gowenrw/hom3c0ming_badge/3D/FlashForgeAdv3/my_flower_profile-09.jpg

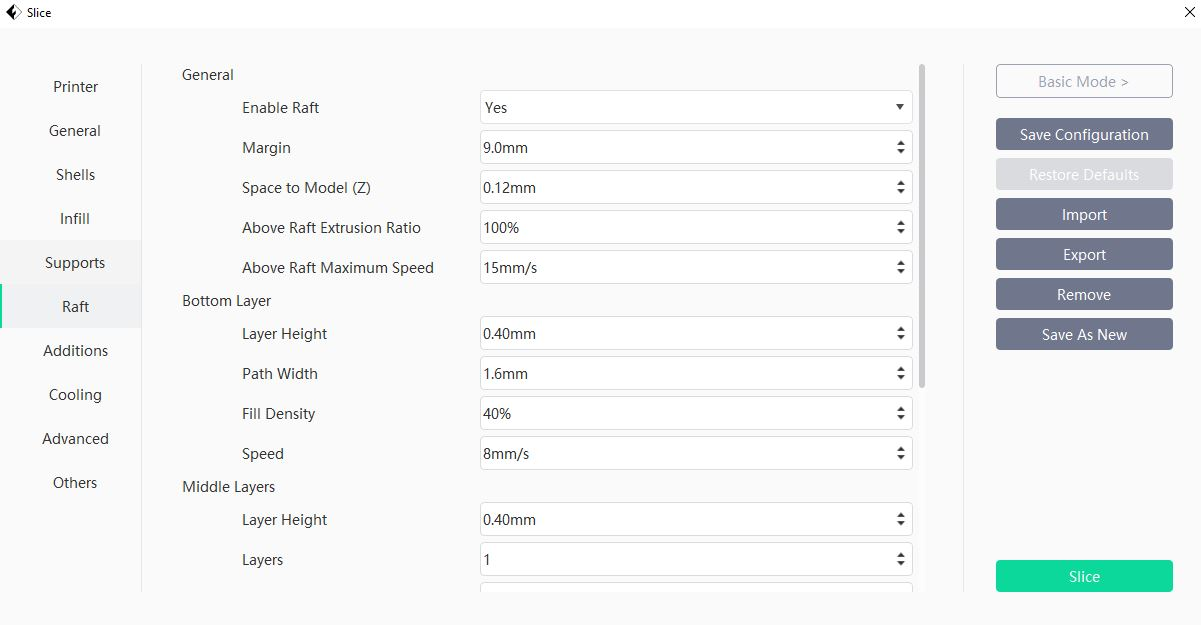
3D/FlashForgeAdv3/my_flower_profile-09.jpg
