gowenrw/hom3c0ming_badge/3D/Rose_LED_Cover_w_Leaves_back.jpg

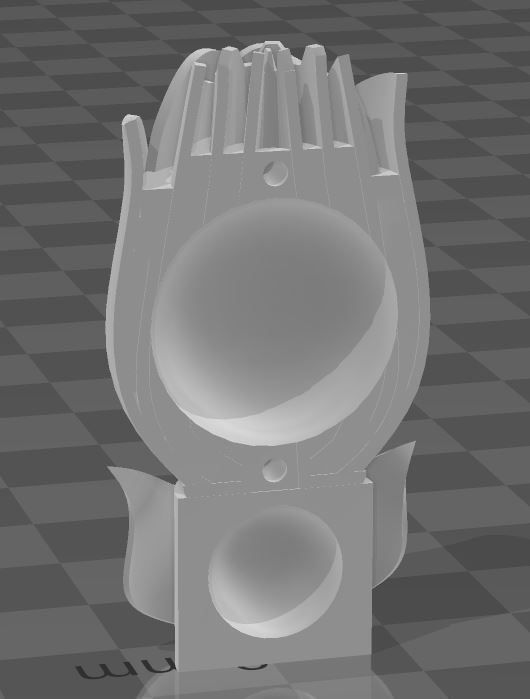
3D/Rose_LED_Cover_w_Leaves_back.jpg
