gowenrw/hom3c0ming_badge/3D/Rose_LED_Cover_w_Leaves_front.jpg

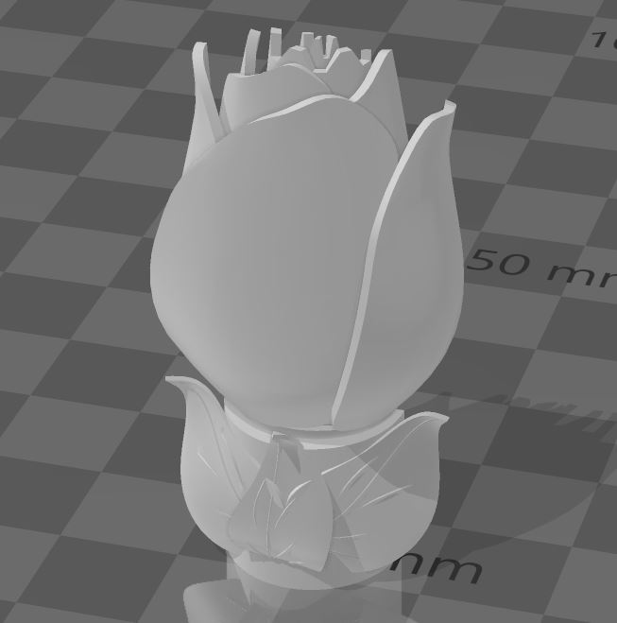
3D/Rose_LED_Cover_w_Leaves_front.jpg
