gowenrw/hom3c0ming_badge/art/Boutonniere_front-1-01.jpg

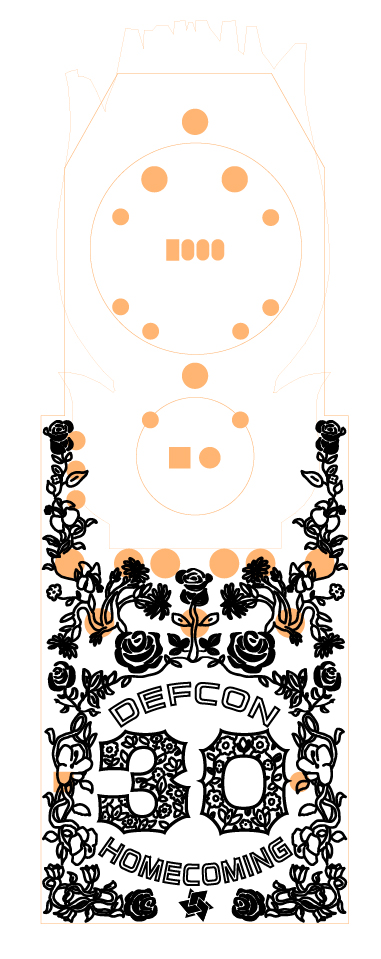
art/Boutonniere_front-1-01.jpg
