gowenrw/hom3c0ming_badge/art/Corsage_front-1-FlowerFace.jpg

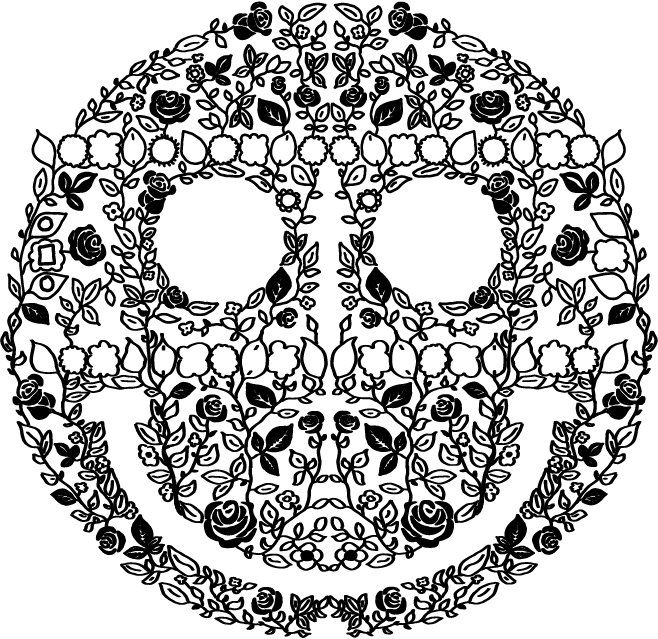
art/Corsage_front-1-FlowerFace.jpg
