gowenrw/hom3c0ming_badge/art/Corsage_front-2-HomeComing.jpg

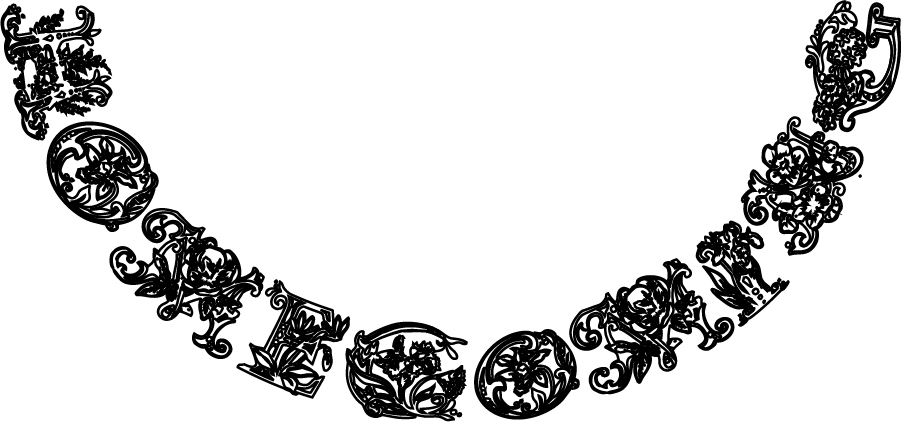
art/Corsage_front-2-HomeComing.jpg
