gowenrw/hom3c0ming_badge/art/Corsage_front-3-MLine.jpg

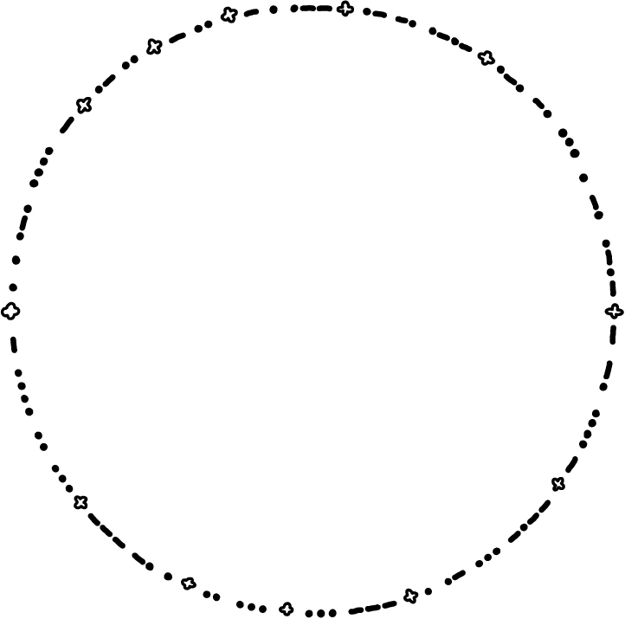
art/Corsage_front-3-MLine.jpg
