gowenrw/hom3c0ming_badge/art/Corsage_front-4-FlowersRightSide.jpg

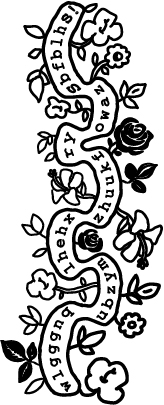
art/Corsage_front-4-FlowersRightSide.jpg
