gowenrw/hom3c0ming_badge/art/Corsage_front-5-FlowersBottom.jpg

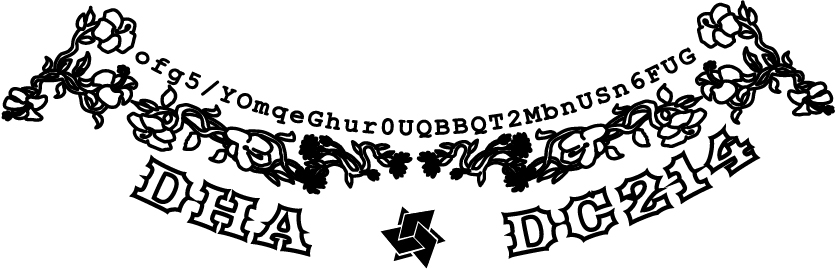
art/Corsage_front-5-FlowersBottom.jpg
