gowenrw/hom3c0ming_badge/art/Elliott_Flowers_2022-06-14_163128.jpg

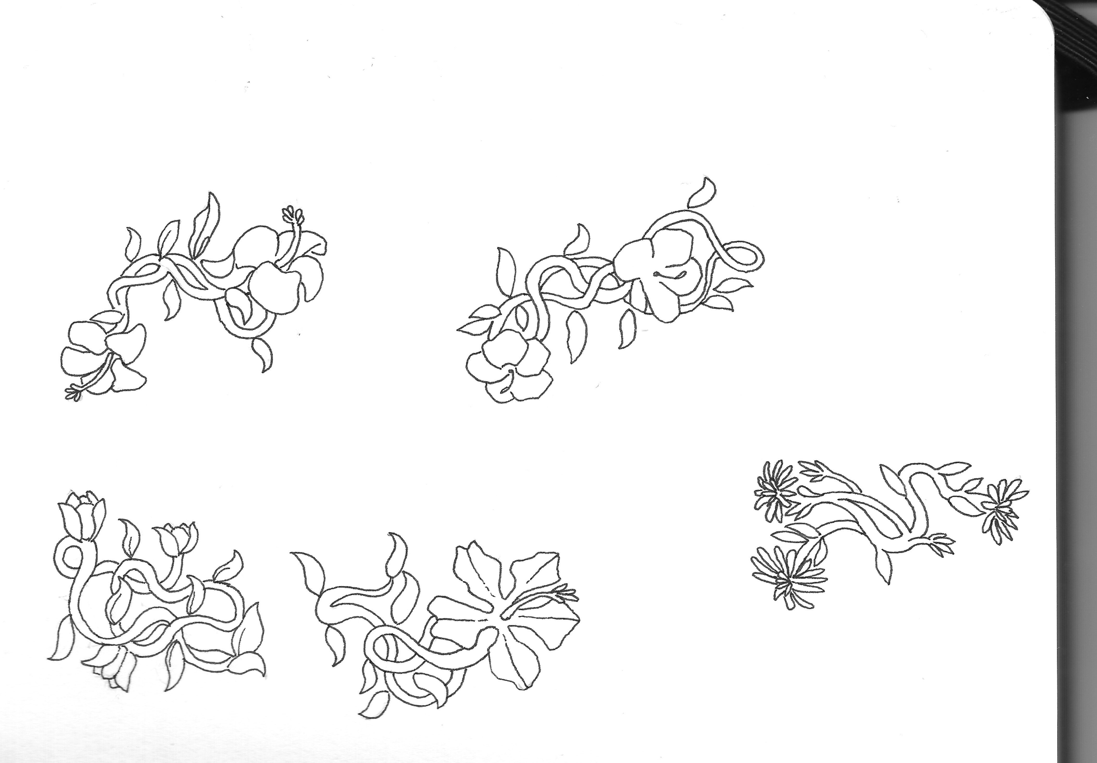
art/Elliott_Flowers_2022-06-14_163128.jpg
