gowenrw/hom3c0ming_badge/art/Hom3C0ming_Sticker-1-01.jpg

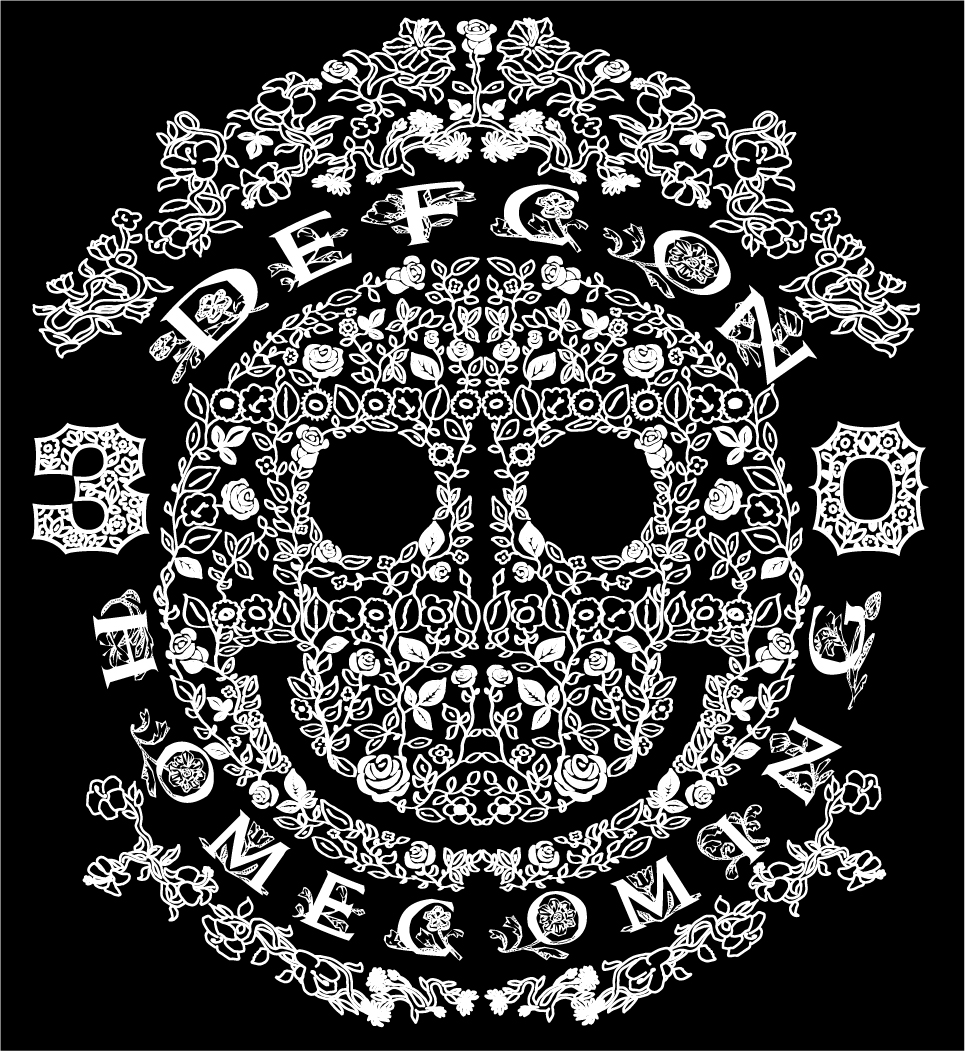
art/Hom3C0ming_Sticker-1-01.jpg
