gowenrw/hom3c0ming_badge/art/Hom3C0ming_Sticker-1PS.png

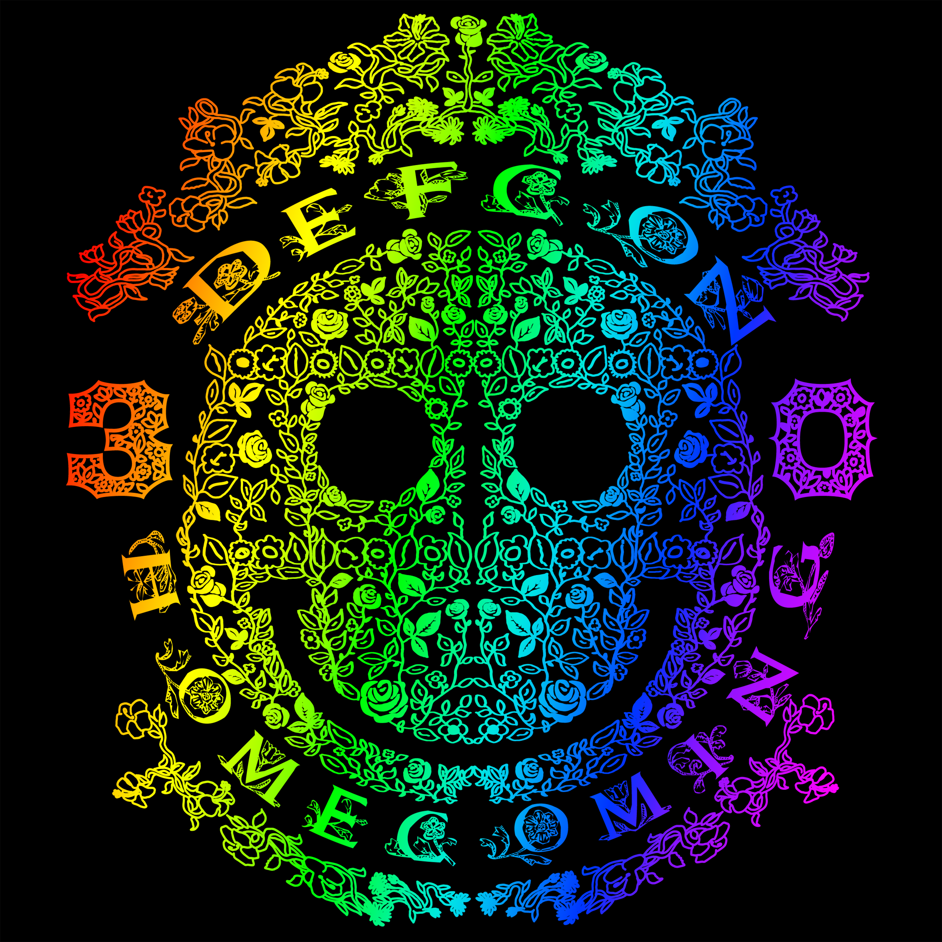
art/Hom3C0ming_Sticker-1PS.png
