gowenrw/hom3c0ming_badge/art/inspiration/20-207884_ivy-vine-drawing-at-getdrawings-ivy-vines-black.png

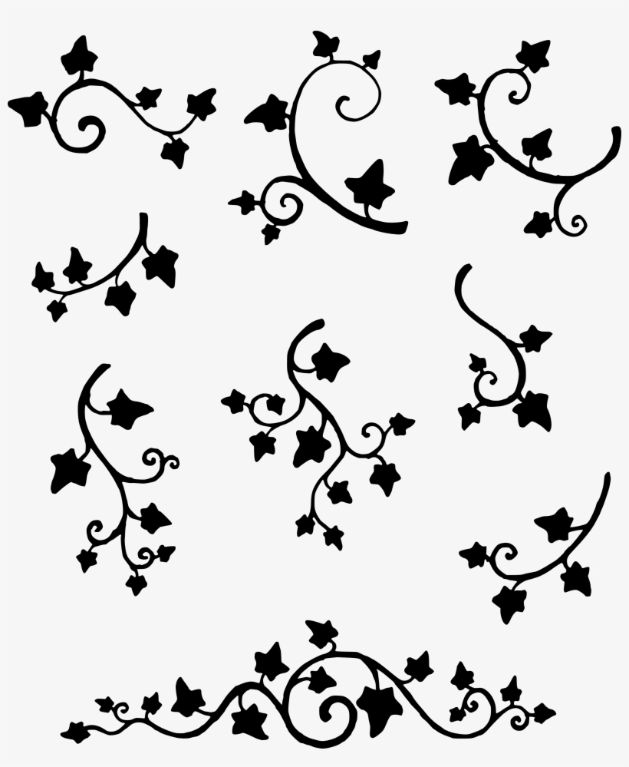
art/inspiration/20-207884_ivy-vine-drawing-at-getdrawings-ivy-vines-black.png
