gowenrw/hom3c0ming_badge/art/inspiration/beautiful-rose-vine-line-art-drawing-on-white-background-2GN6FTX.jpg

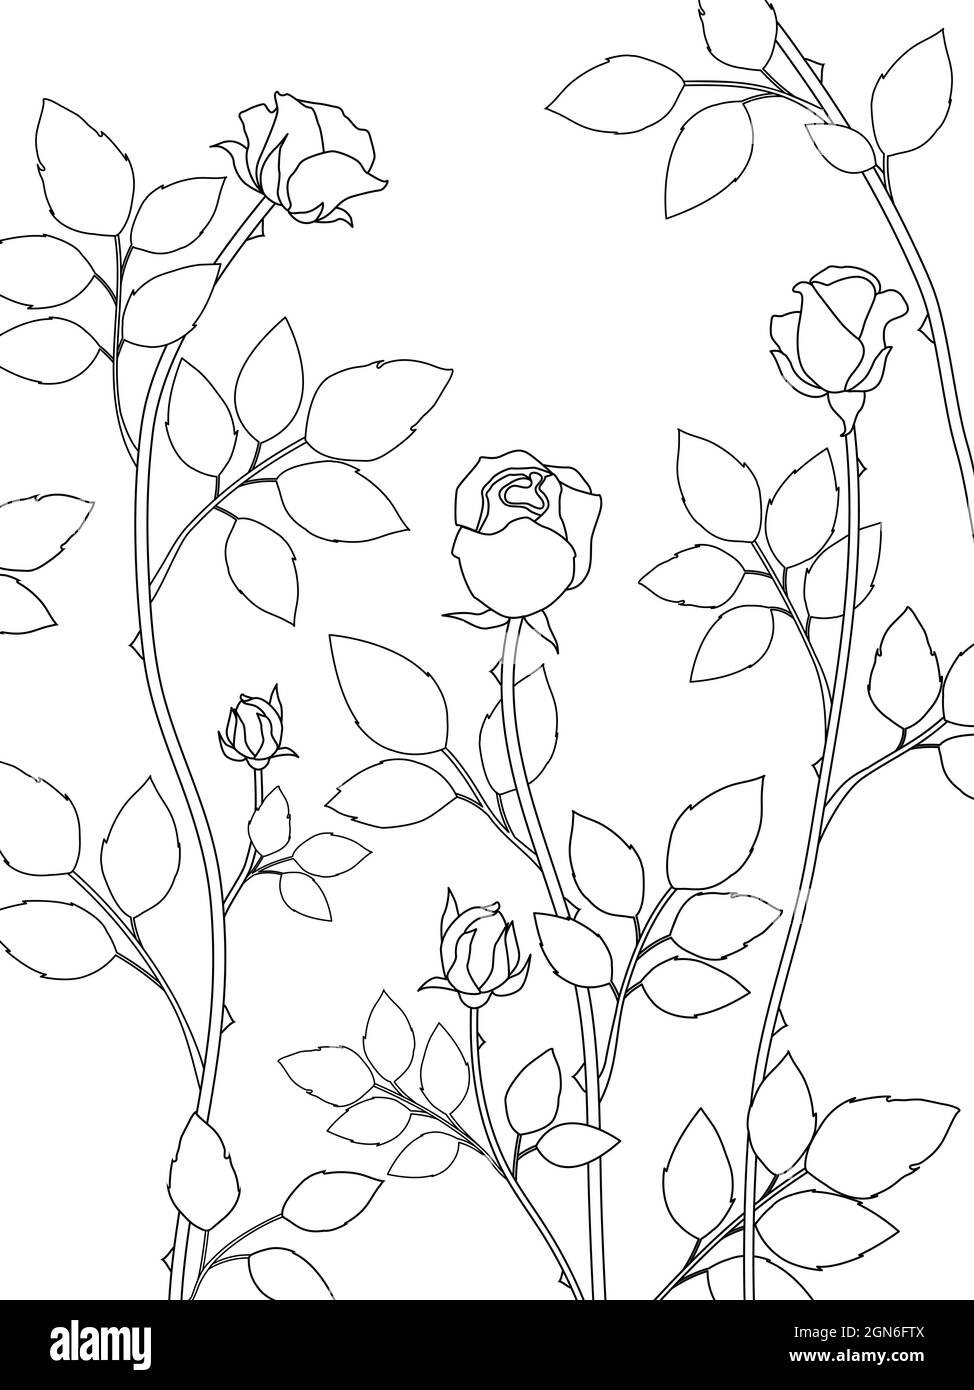
art/inspiration/beautiful-rose-vine-line-art-drawing-on-white-background-2GN6FTX.jpg
