gowenrw/hom3c0ming_badge/art/inspiration/e7fd83ab4b675ca70f8ec98111396026.jpg

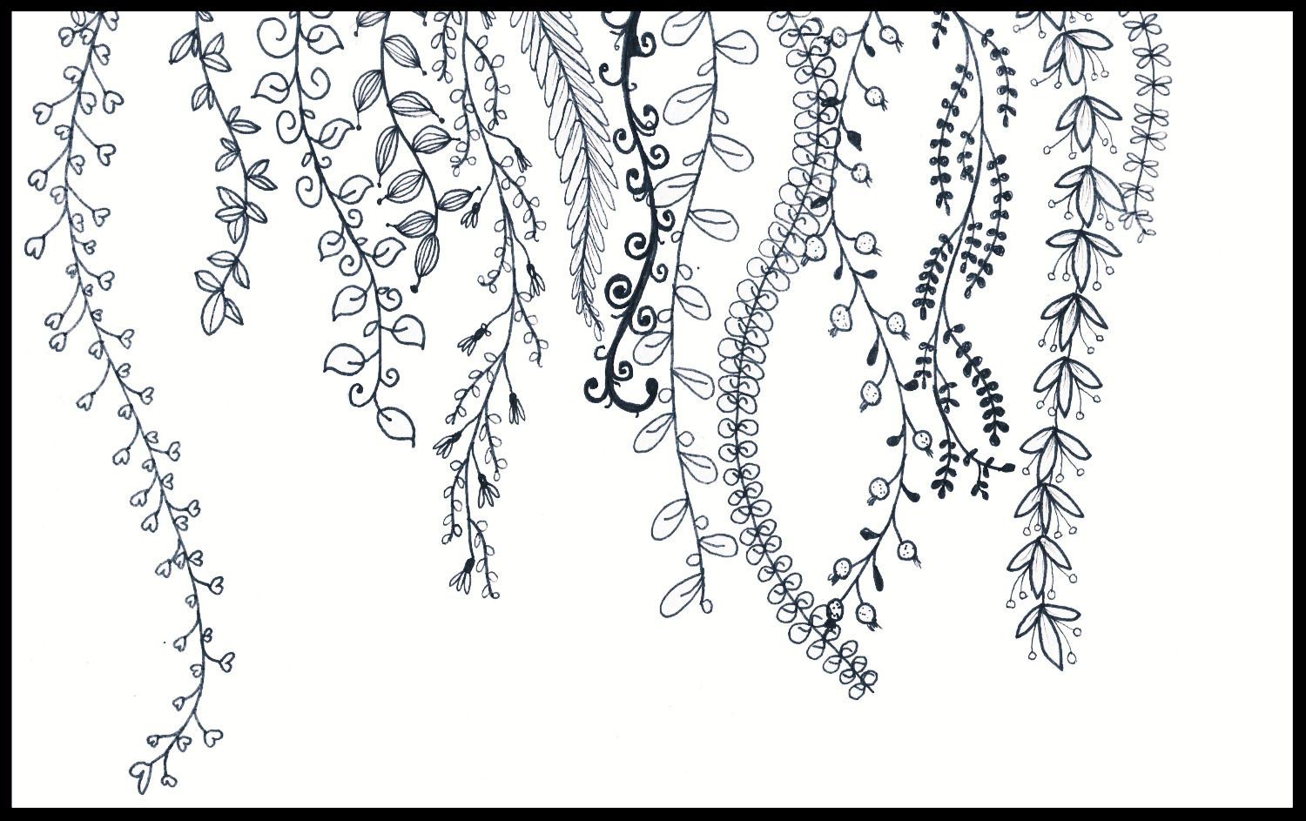
art/inspiration/e7fd83ab4b675ca70f8ec98111396026.jpg
