gowenrw/hom3c0ming_badge/art/inspiration/images.png

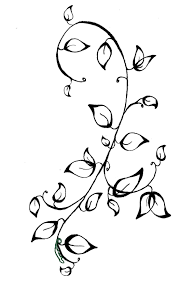
art/inspiration/images.png
