gowenrw/hom3c0ming_badge/art/Lanyard_Proof-uspv-62c86421a04712112495465-1657300001.png

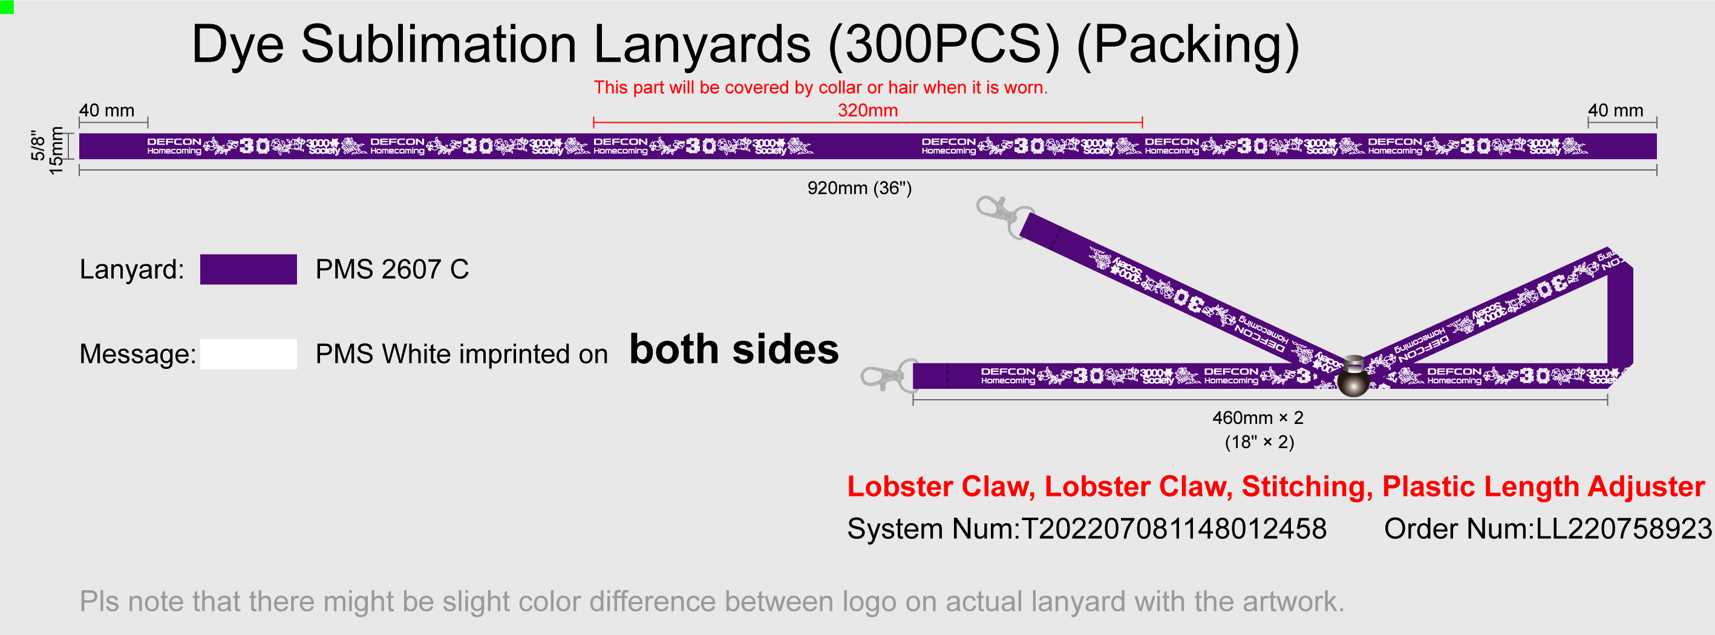
art/Lanyard_Proof-uspv-62c86421a04712112495465-1657300001.png
