gowenrw/hom3c0ming_badge/docs/images/20220730_111540-DatA55.jpg

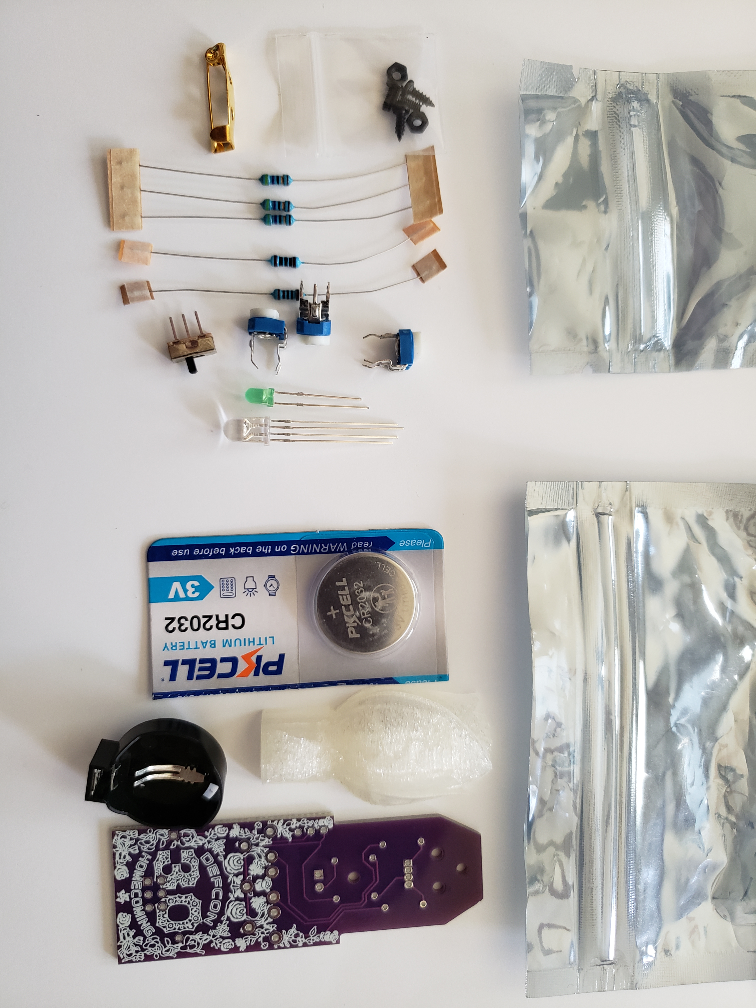
docs/images/20220730_111540-DatA55.jpg
