gowenrw/hom3c0ming_badge/eda/hom3c0ming_boutonniere/snapshots/hom3c0ming_boutonniere_back.jpg

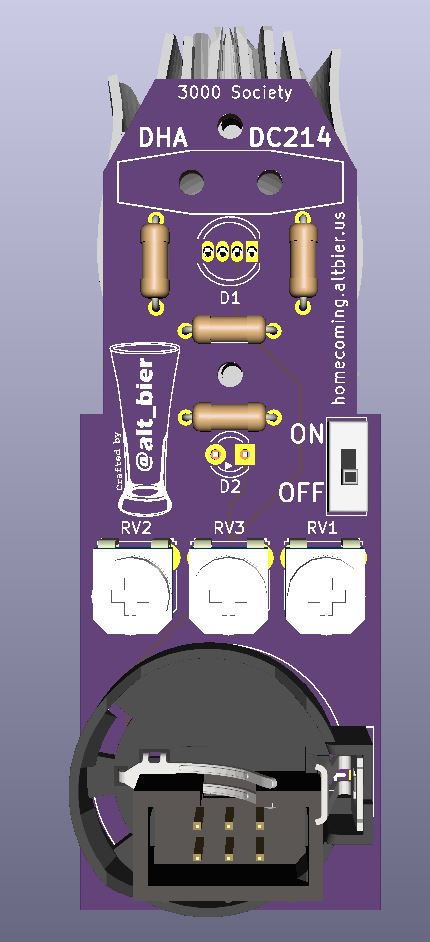
eda/hom3c0ming_boutonniere/snapshots/hom3c0ming_boutonniere_back.jpg
