gowenrw/hom3c0ming_badge/eda/hom3c0ming_corsage/snapshots/20220705_151704.jpg

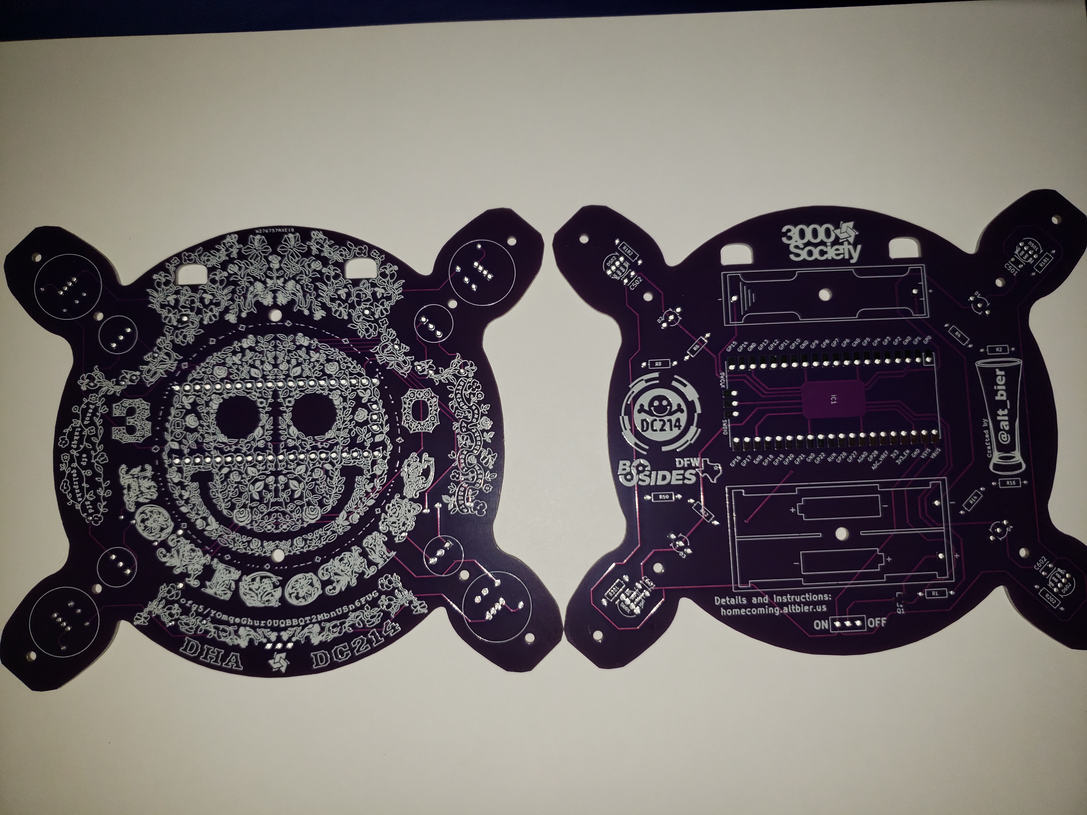
eda/hom3c0ming_corsage/snapshots/20220705_151704.jpg
