gowenrw/hom3c0ming_badge/eda/hom3c0ming_corsage/snapshots/hom3c0ming_corsage_back.jpg

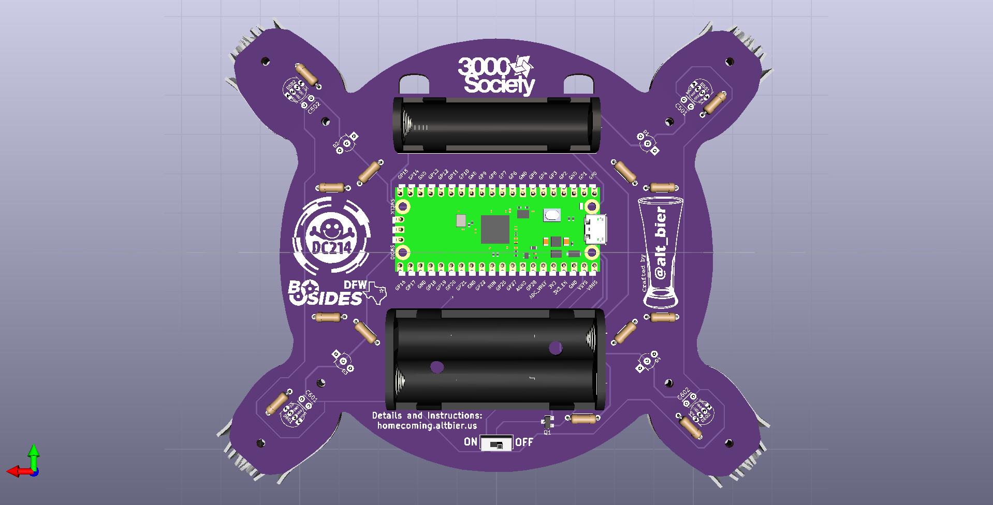
eda/hom3c0ming_corsage/snapshots/hom3c0ming_corsage_back.jpg
