gowenrw/hom3c0ming_badge/eda/hom3c0ming_boutonniere/3d_models/PinHeader_1x08_P2.54mm_Horizontal.step

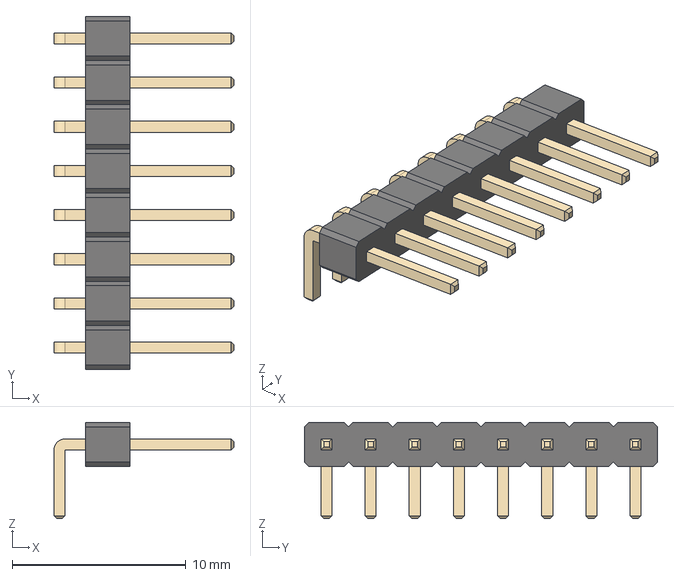
[picture p76: CAD file, 2022-07-30]
eda/hom3c0ming_boutonniere/3d_models/PinHeader_1x08_P2.54mm_Horizontal.step
10.4 x 20.3 x 5.54 mm
