gowenrw/hom3c0ming_badge/eda/hom3c0ming_corsage/3d_models/C_Rect_L4.6mm_W2.0mm_P2.50mm_MKS02_FKP02.step

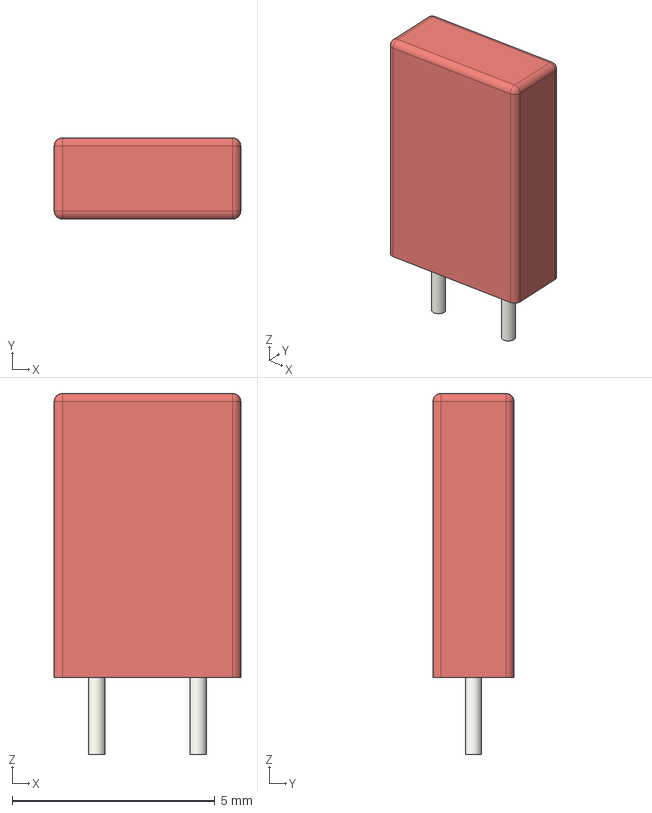
[picture p77: CAD file, 2022-07-30]
eda/hom3c0ming_corsage/3d_models/C_Rect_L4.6mm_W2.0mm_P2.50mm_MKS02_FKP02.step
4.60 x 2.00 x 8.90 mm
