gowenrw/hom3c0ming_badge/art/Corsage_front-5-FlowersBottom.dxf

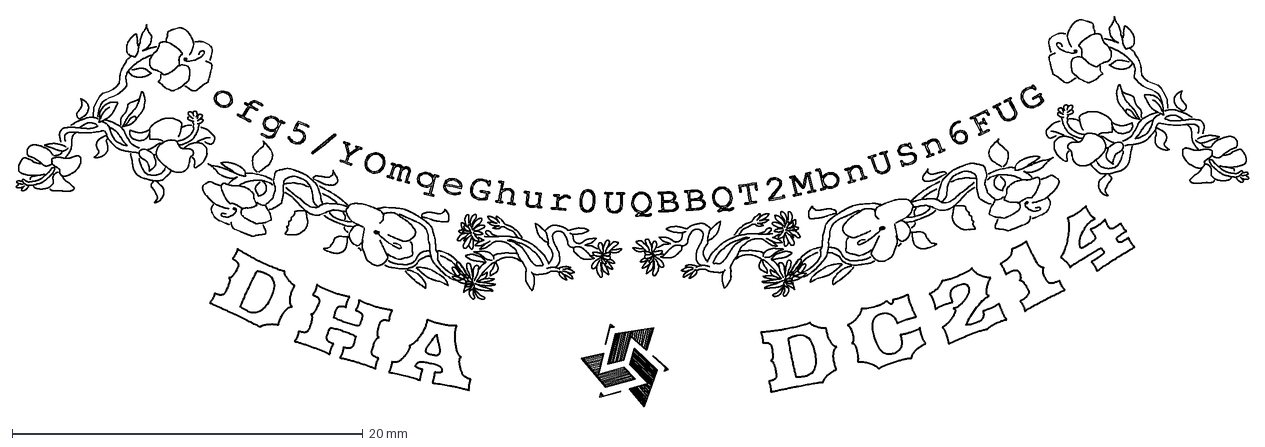
[picture p78: CAD file, 2022-07-30]
art/Corsage_front-5-FlowersBottom.dxf
70.3 x 22.3 mm
