gowenrw/hom3c0ming_badge/eda/hom3c0ming_boutonniere/3d_models/SOT-23.step

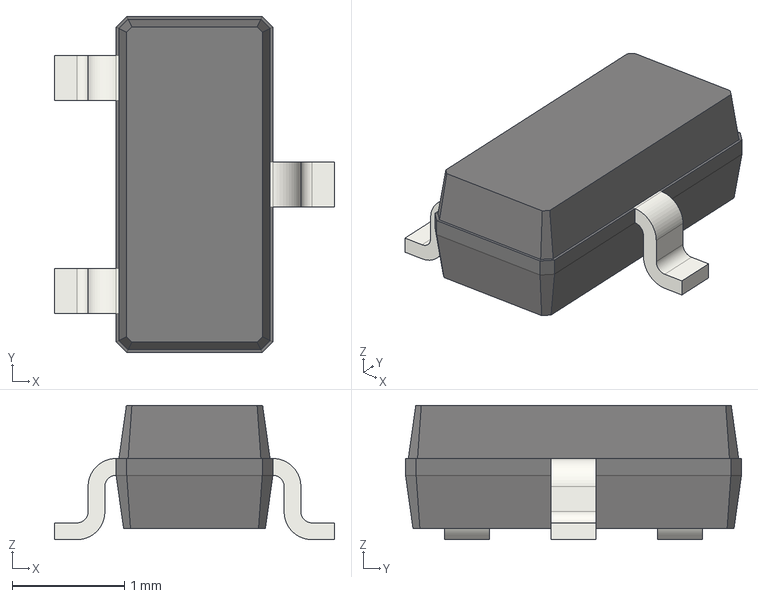
[picture p79: CAD file, 2022-07-30]
eda/hom3c0ming_boutonniere/3d_models/SOT-23.step
2.50 x 3.00 x 1.20 mm
