gowenrw/hom3c0ming_badge/eda/hom3c0ming_corsage/3d_models/LED_0805_2012Metric_Castellated.step

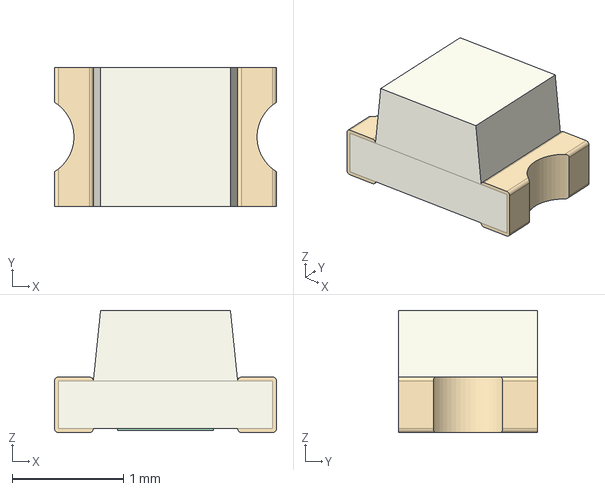
[picture p80: CAD file, 2022-07-30]
eda/hom3c0ming_corsage/3d_models/LED_0805_2012Metric_Castellated.step
2.00 x 1.25 x 1.10 mm
