gowenrw/hom3c0ming_badge/eda/hom3c0ming_boutonniere/3d_models/LED_D8.0mm.step

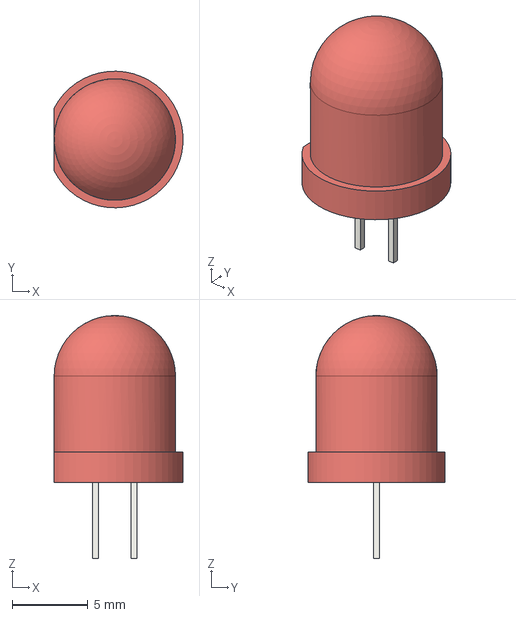
[picture p81: CAD file, 2022-07-30]
eda/hom3c0ming_boutonniere/3d_models/LED_D8.0mm.step
8.49 x 9.00 x 16.0 mm
