gowenrw/hom3c0ming_badge/eda/hom3c0ming_corsage/3d_models/SW_PUSH_6mm.step

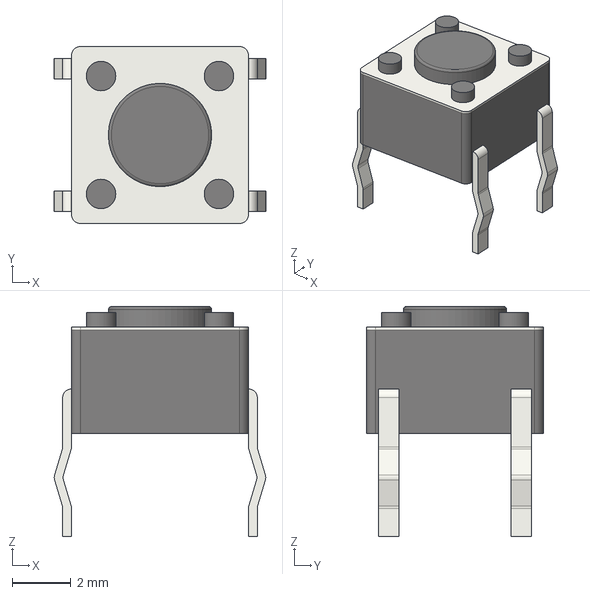
[picture p82: CAD file, 2022-07-30]
eda/hom3c0ming_corsage/3d_models/SW_PUSH_6mm.step
7.17 x 6.00 x 7.80 mm
