gowenrw/hom3c0ming_badge/eda/hom3c0ming_corsage/3d_models/PinSocket_1x05_P2.54mm_Horizontal.step

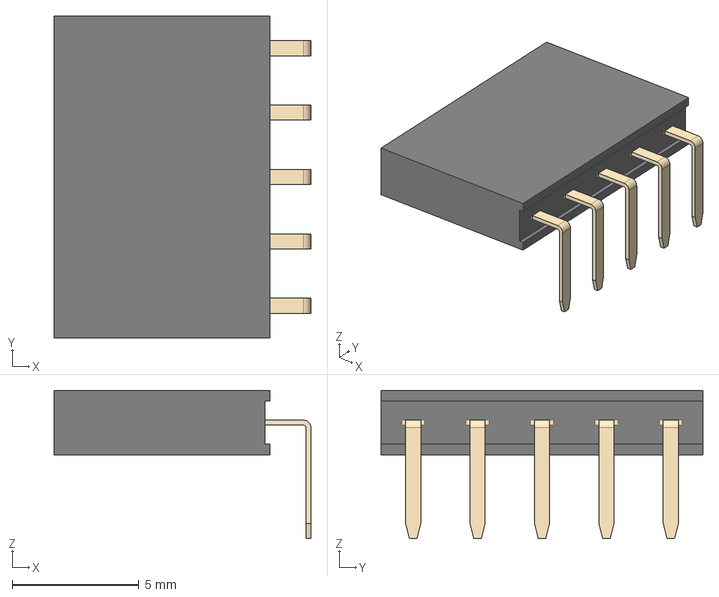
[picture p84: CAD file, 2022-07-30]
eda/hom3c0ming_corsage/3d_models/PinSocket_1x05_P2.54mm_Horizontal.step
10.1 x 12.7 x 5.84 mm
