gowenrw/hom3c0ming_badge/eda/hom3c0ming_boutonniere/3d_models/PinHeader_1x07_P2.54mm_Vertical.step

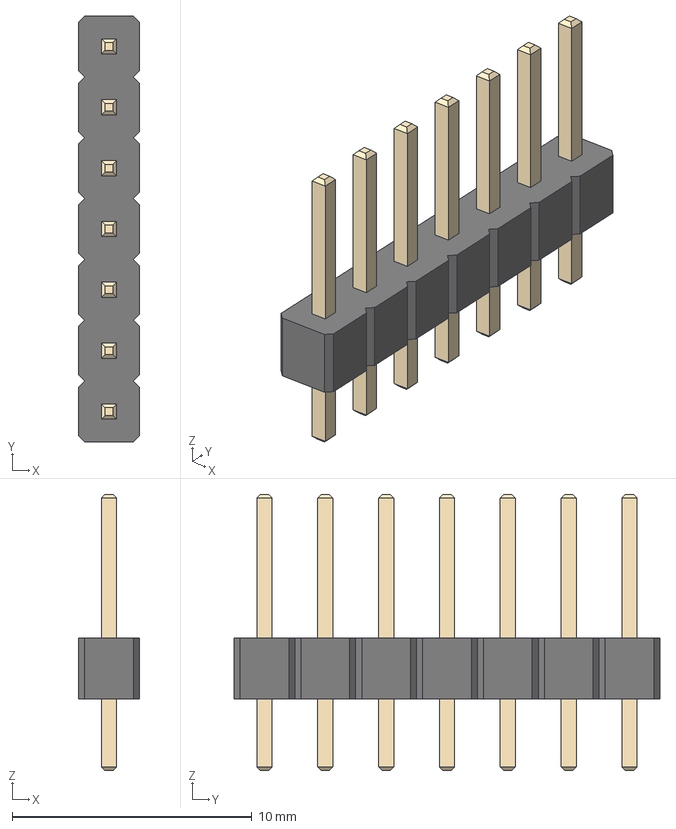
[picture p85: CAD file, 2022-07-30]
eda/hom3c0ming_boutonniere/3d_models/PinHeader_1x07_P2.54mm_Vertical.step
2.54 x 17.8 x 11.5 mm
