gowenrw/hom3c0ming_badge/eda/hom3c0ming_corsage/3d_models/PinHeader_1x07_P2.54mm_Horizontal.step

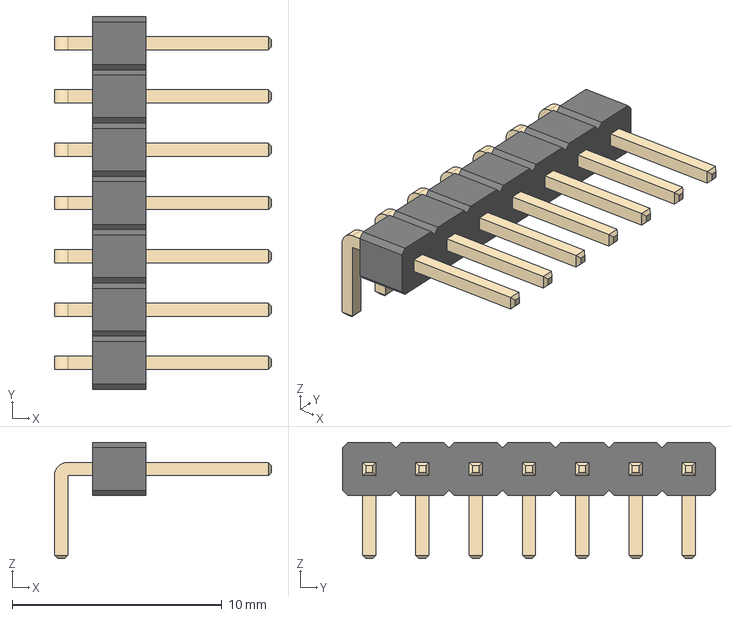
[picture p86: CAD file, 2022-07-30]
eda/hom3c0ming_corsage/3d_models/PinHeader_1x07_P2.54mm_Horizontal.step
10.4 x 17.8 x 5.54 mm
