gowenrw/hom3c0ming_badge/eda/hom3c0ming_boutonniere/3d_models/PinHeader_1x10_P2.54mm_Horizontal.step

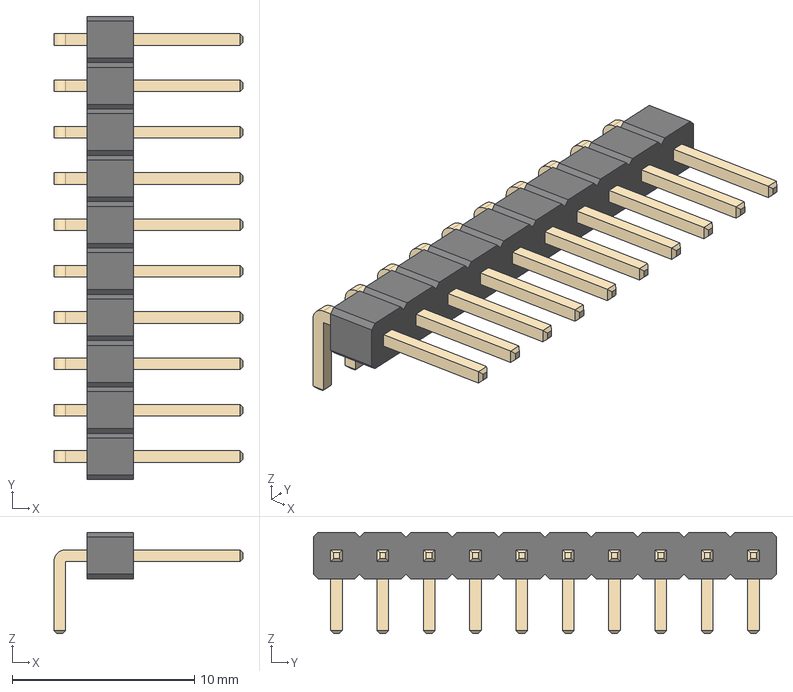
[picture p87: CAD file, 2022-07-30]
eda/hom3c0ming_boutonniere/3d_models/PinHeader_1x10_P2.54mm_Horizontal.step
10.4 x 25.4 x 5.54 mm
