gowenrw/hom3c0ming_badge/eda/hom3c0ming_boutonniere/3d_models/PinHeader_1x20_P2.54mm_Vertical.step

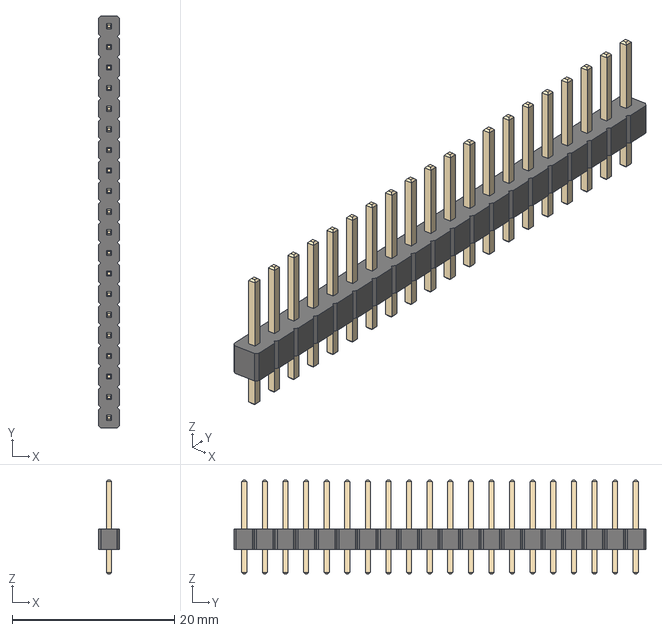
[picture p88: CAD file, 2022-07-30]
eda/hom3c0ming_boutonniere/3d_models/PinHeader_1x20_P2.54mm_Vertical.step
2.54 x 50.8 x 11.5 mm
