gowenrw/hom3c0ming_badge/eda/hom3c0ming_corsage/3d_models/PinHeader_1x06_P2.54mm_Horizontal.step

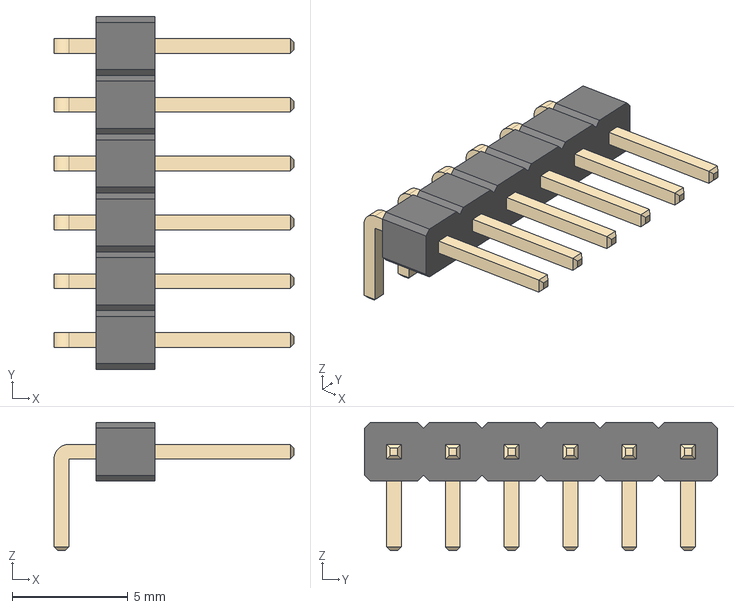
[picture p89: CAD file, 2022-07-30]
eda/hom3c0ming_corsage/3d_models/PinHeader_1x06_P2.54mm_Horizontal.step
10.4 x 15.2 x 5.54 mm
