gowenrw/hom3c0ming_badge/eda/hom3c0ming_corsage/3d_models/C_Disc_D3.0mm_W2.0mm_P2.50mm.step

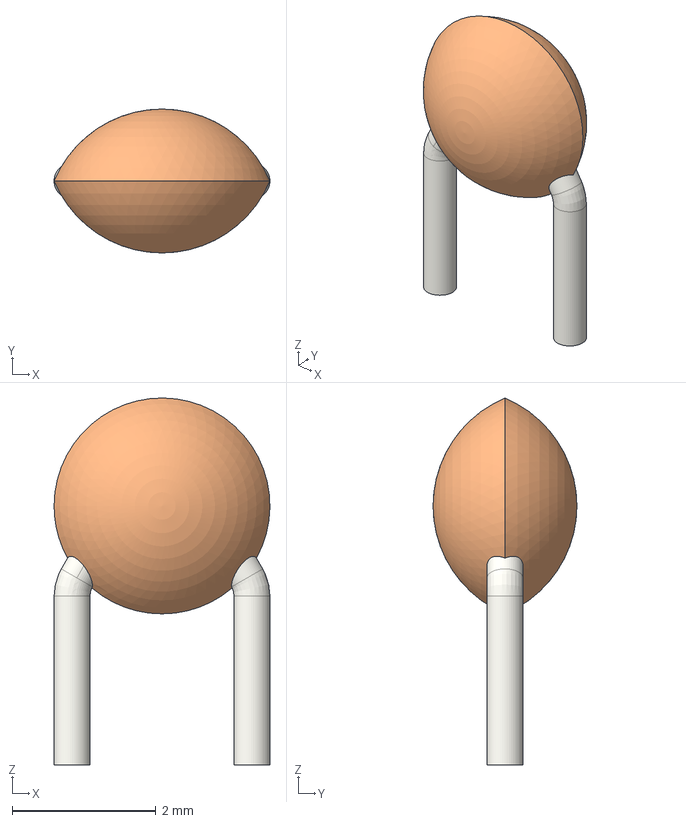
[picture p91: CAD file, 2022-07-30]
eda/hom3c0ming_corsage/3d_models/C_Disc_D3.0mm_W2.0mm_P2.50mm.step
3.00 x 2.00 x 5.10 mm
