gowenrw/hom3c0ming_badge/eda/hom3c0ming_corsage/3d_models/PinHeader_1x03_P2.54mm_Horizontal.step

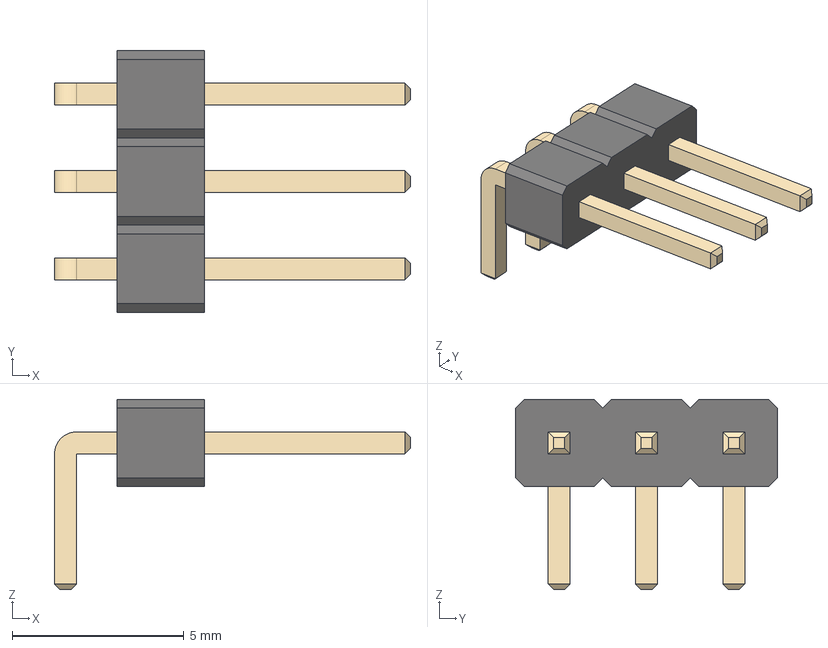
[picture p92: CAD file, 2022-07-30]
eda/hom3c0ming_corsage/3d_models/PinHeader_1x03_P2.54mm_Horizontal.step
10.4 x 7.62 x 5.54 mm
