gowenrw/hom3c0ming_badge/eda/hom3c0ming_corsage/3d_models/R_Axial_DIN0204_L3.6mm_D1.6mm_P5.08mm_Horizontal.step

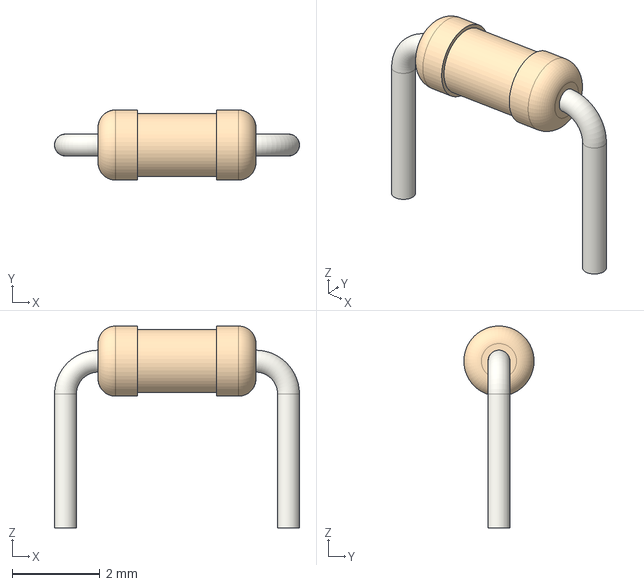
[picture p94: CAD file, 2022-07-30]
eda/hom3c0ming_corsage/3d_models/R_Axial_DIN0204_L3.6mm_D1.6mm_P5.08mm_Horizontal.step
5.58 x 1.60 x 4.60 mm
