gowenrw/hom3c0ming_badge/eda/hom3c0ming_corsage/3d_models/LED_1206_3216Metric_Castellated.step

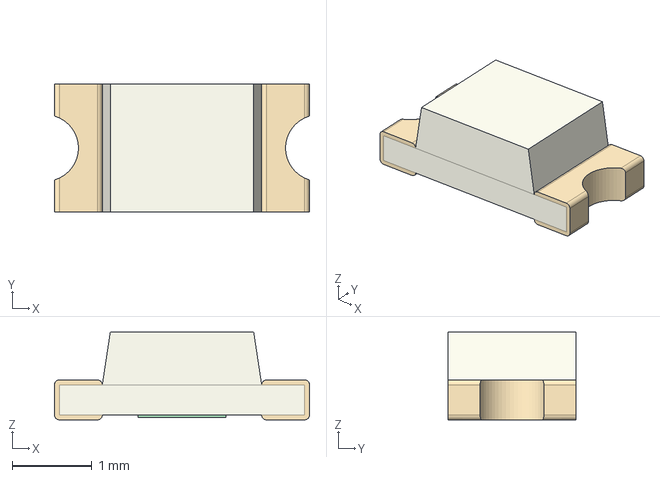
[picture p98: CAD file, 2022-07-30]
eda/hom3c0ming_corsage/3d_models/LED_1206_3216Metric_Castellated.step
3.20 x 1.60 x 1.10 mm
