gowenrw/hom3c0ming_badge/eda/hom3c0ming_boutonniere/3d_models/C_1206_3216Metric.step

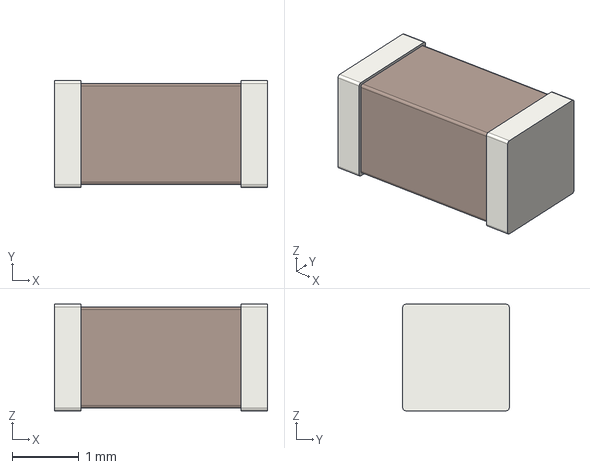
[picture p99: CAD file, 2022-07-30]
eda/hom3c0ming_boutonniere/3d_models/C_1206_3216Metric.step
3.20 x 1.60 x 1.60 mm
