gowenrw/hom3c0ming_badge/eda/hom3c0ming_corsage/3d_models/R_0805_2012Metric.step

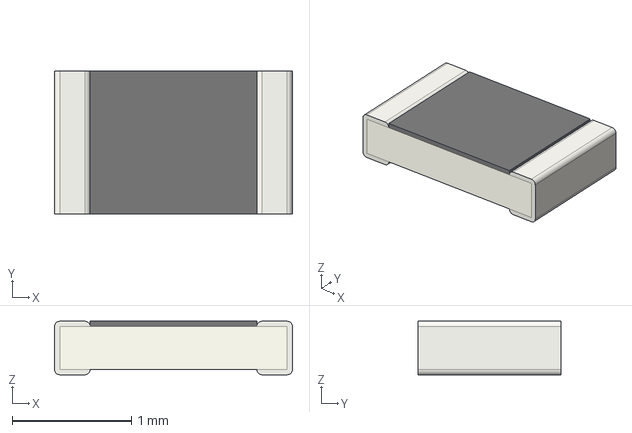
[picture p100: CAD file, 2022-07-30]
eda/hom3c0ming_corsage/3d_models/R_0805_2012Metric.step
2.00 x 1.20 x 0.45 mm
