gowenrw/hom3c0ming_badge/eda/hom3c0ming_corsage/3d_models/PinHeader_1x01_P2.54mm_Vertical.step

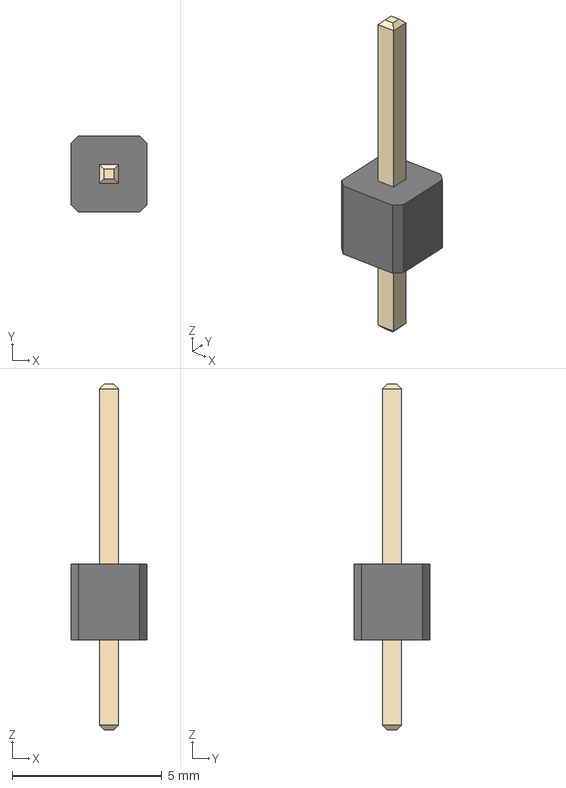
[picture p102: CAD file, 2022-07-30]
eda/hom3c0ming_corsage/3d_models/PinHeader_1x01_P2.54mm_Vertical.step
2.54 x 2.54 x 11.5 mm
