gowenrw/hom3c0ming_badge/eda/hom3c0ming_boutonniere/3d_models/BatteryHolder_2466_1xAAA.step

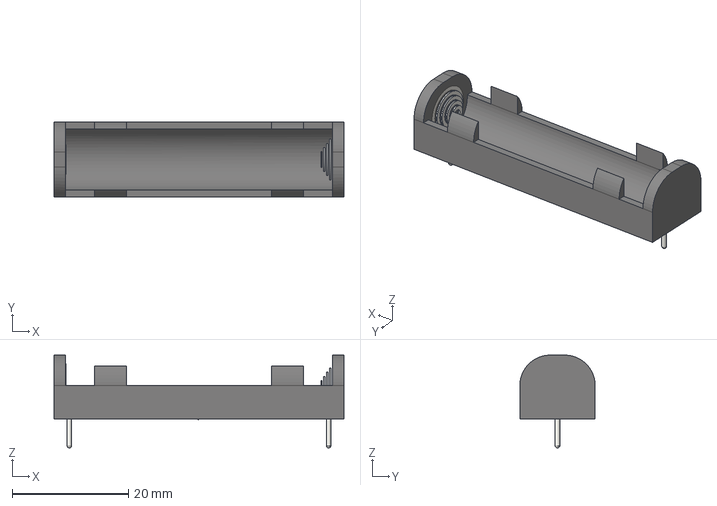
[picture p104: CAD file, 2022-07-30]
eda/hom3c0ming_boutonniere/3d_models/BatteryHolder_2466_1xAAA.step
50.0 x 13.0 x 16.0 mm
