gowenrw/hom3c0ming_badge/eda/hom3c0ming_boutonniere/3d_models/R_Axial_DIN0207_L6.3mm_D2.5mm_P7.62mm_Horizontal.step

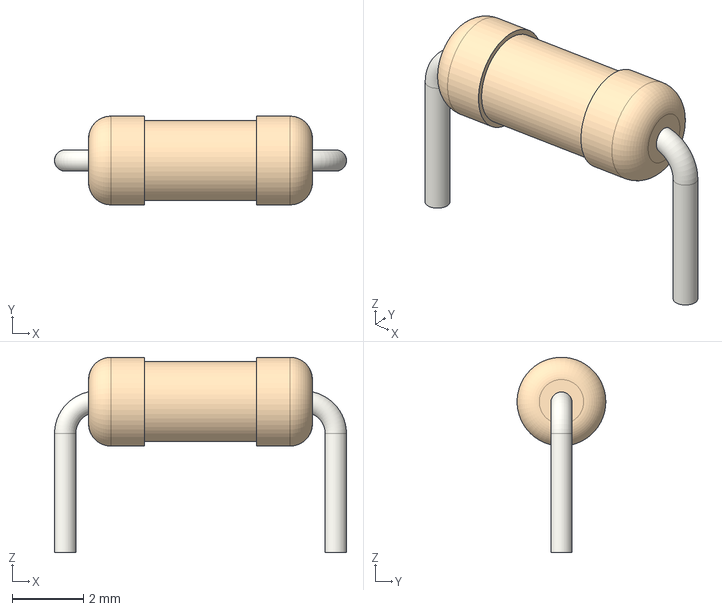
[picture p106: CAD file, 2022-07-30]
eda/hom3c0ming_boutonniere/3d_models/R_Axial_DIN0207_L6.3mm_D2.5mm_P7.62mm_Horizontal.step
8.22 x 2.50 x 5.50 mm
