gowenrw/hom3c0ming_badge/eda/hom3c0ming_corsage/3d_models/Battery_Holder_CR2032_BS-2-1.stp

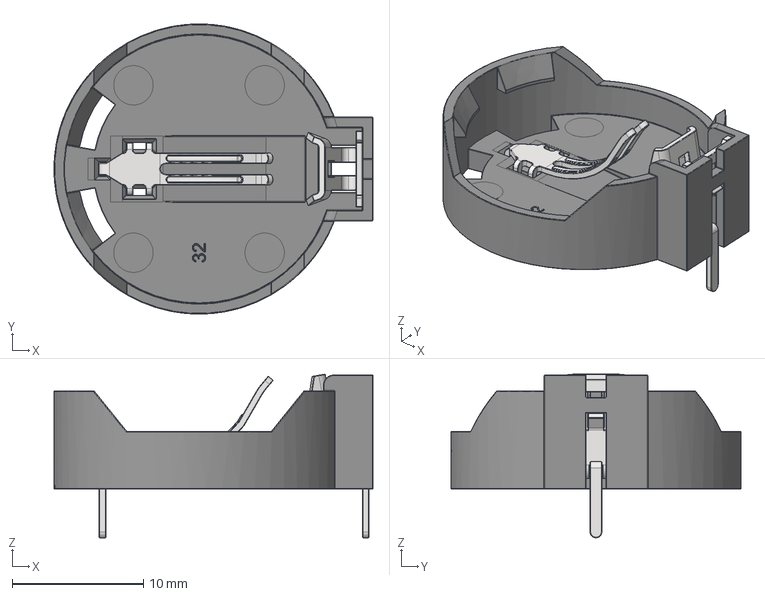
[picture p107: CAD file, 2022-07-30]
eda/hom3c0ming_corsage/3d_models/Battery_Holder_CR2032_BS-2-1.stp
24.3 x 22.1 x 12.5 mm
