gowenrw/hom3c0ming_badge/eda/hom3c0ming_corsage/3d_models/CP_Radial_D6.3mm_P2.50mm.step

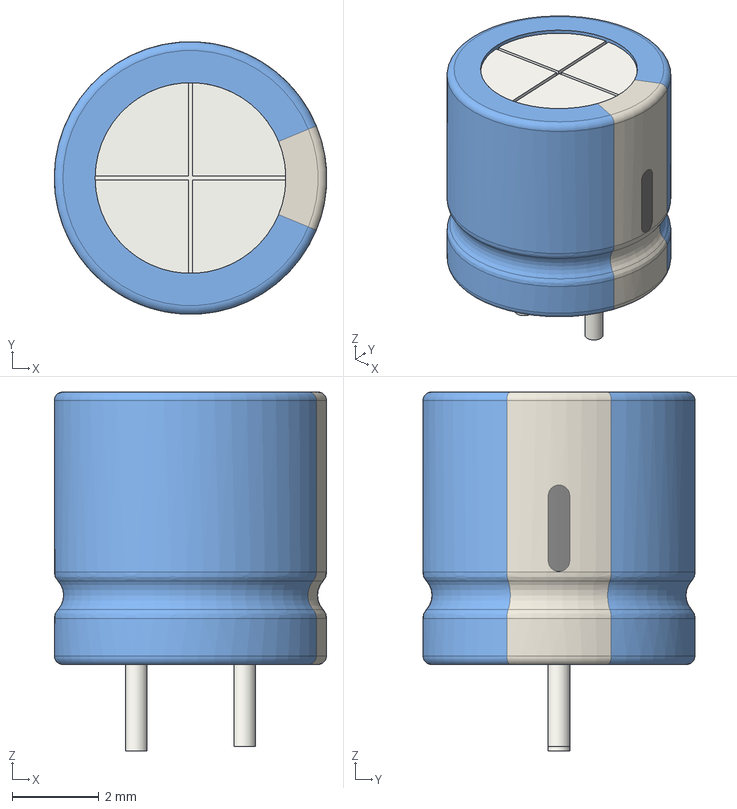
[picture p108: CAD file, 2022-07-30]
eda/hom3c0ming_corsage/3d_models/CP_Radial_D6.3mm_P2.50mm.step
6.30 x 6.30 x 8.30 mm
