gowenrw/hom3c0ming_badge/eda/hom3c0ming_corsage/3d_models/LED_D3.0mm-3.step

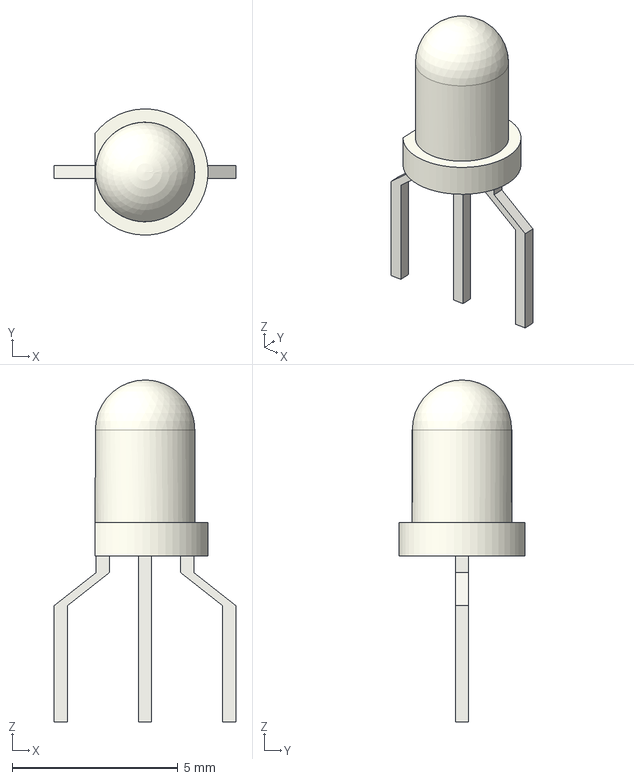
[picture p111: CAD file, 2022-07-30]
eda/hom3c0ming_corsage/3d_models/LED_D3.0mm-3.step
5.48 x 3.80 x 10.3 mm
