gowenrw/hom3c0ming_badge/eda/hom3c0ming_corsage/3d_models/TS2306A.step

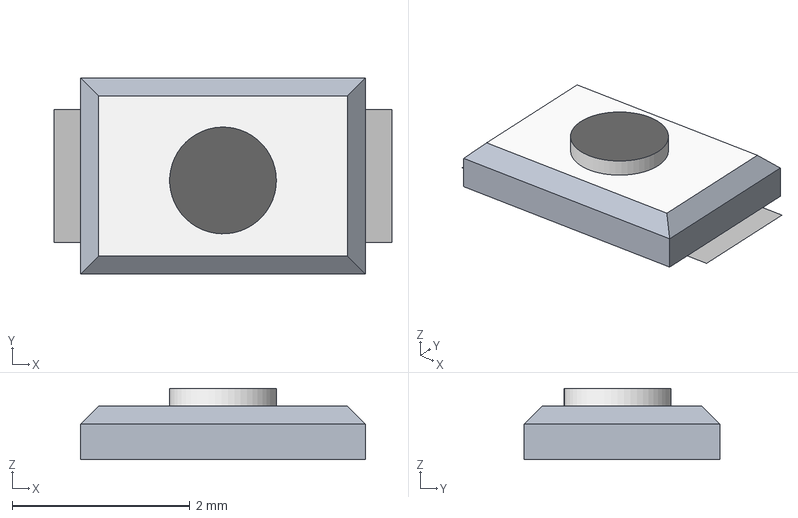
[picture p112: CAD file, 2022-07-30]
eda/hom3c0ming_corsage/3d_models/TS2306A.step
3.80 x 2.20 x 0.8 mm
Plane
