gowenrw/hom3c0ming_badge/eda/hom3c0ming_boutonniere/3d_models/PinSocket_1x02_P2.54mm_Horizontal.step

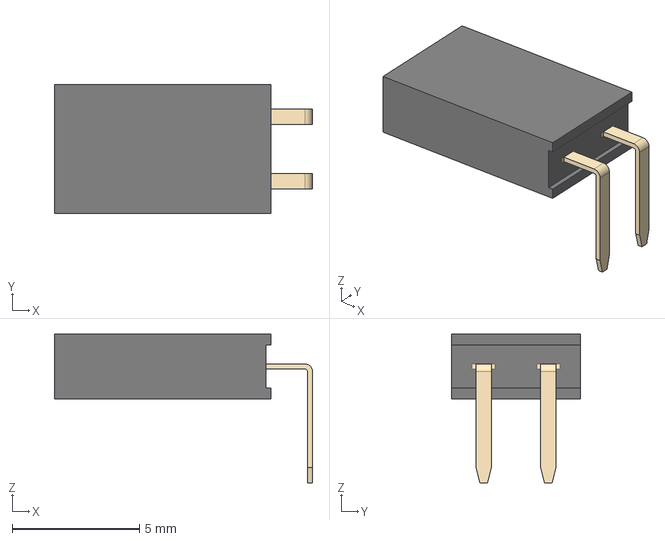
[picture p113: CAD file, 2022-07-30]
eda/hom3c0ming_boutonniere/3d_models/PinSocket_1x02_P2.54mm_Horizontal.step
10.1 x 5.08 x 5.84 mm
