gowenrw/hom3c0ming_badge/eda/hom3c0ming_corsage/3d_models/CP_Radial_D5.0mm_P2.00mm.step

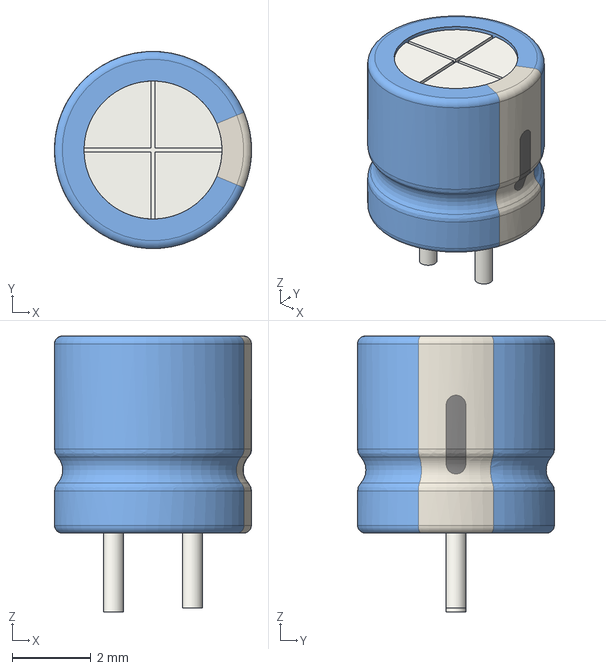
[picture p114: CAD file, 2022-07-30]
eda/hom3c0ming_corsage/3d_models/CP_Radial_D5.0mm_P2.00mm.step
5.00 x 5.00 x 7.00 mm
