gowenrw/hom3c0ming_badge/eda/hom3c0ming_boutonniere/3d_models/RJ45_Amphenol_RJHSE538X.step

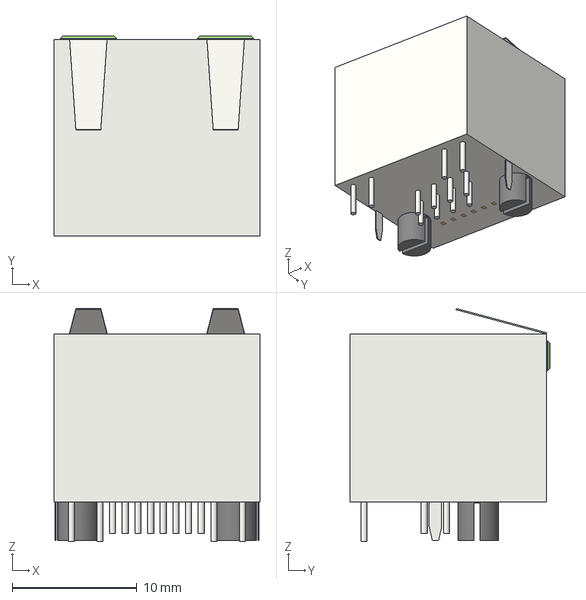
[picture p115: CAD file, 2022-07-30]
eda/hom3c0ming_boutonniere/3d_models/RJ45_Amphenol_RJHSE538X.step
16.5 x 16.1 x 18.7 mm
