gowenrw/hom3c0ming_badge/eda/hom3c0ming_corsage/3d_models/RJ45_Amphenol_RJHSE-5080-56544.STEP

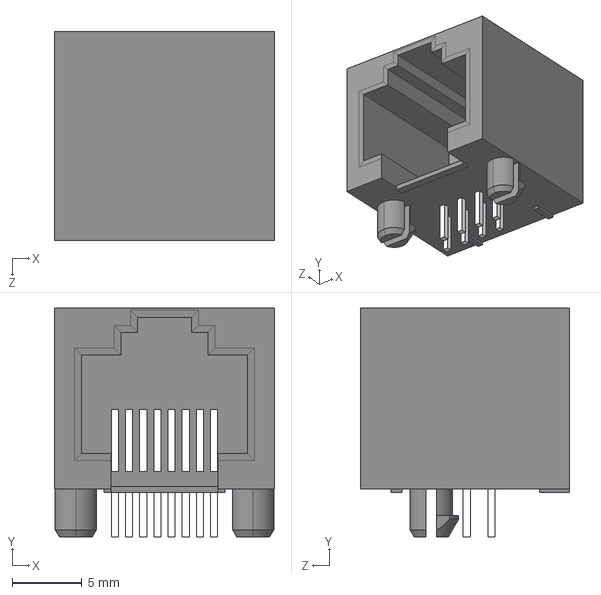
[picture p116: CAD file, 2022-07-30]
eda/hom3c0ming_corsage/3d_models/RJ45_Amphenol_RJHSE-5080-56544.STEP
15.7 x 16.4 x 15.0 mm
