gowenrw/hom3c0ming_badge/eda/hom3c0ming_boutonniere/3d_models/C_0603_1608Metric.step

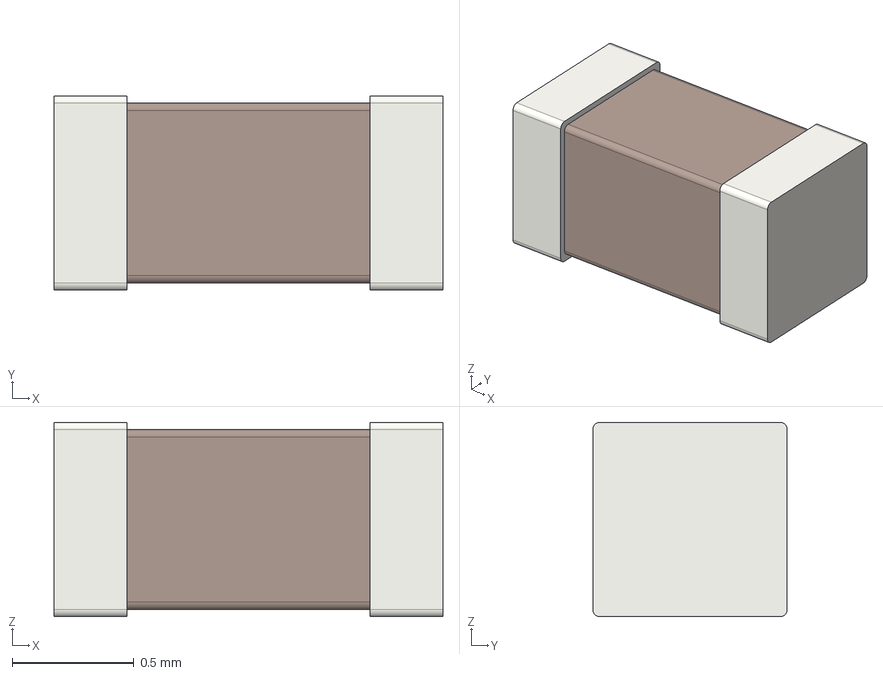
[picture p117: CAD file, 2022-07-30]
eda/hom3c0ming_boutonniere/3d_models/C_0603_1608Metric.step
1.60 x 0.8 x 0.8 mm
