gowenrw/hom3c0ming_badge/eda/hom3c0ming_boutonniere/3d_models/PinSocket_1x02_P2.54mm_Vertical.step

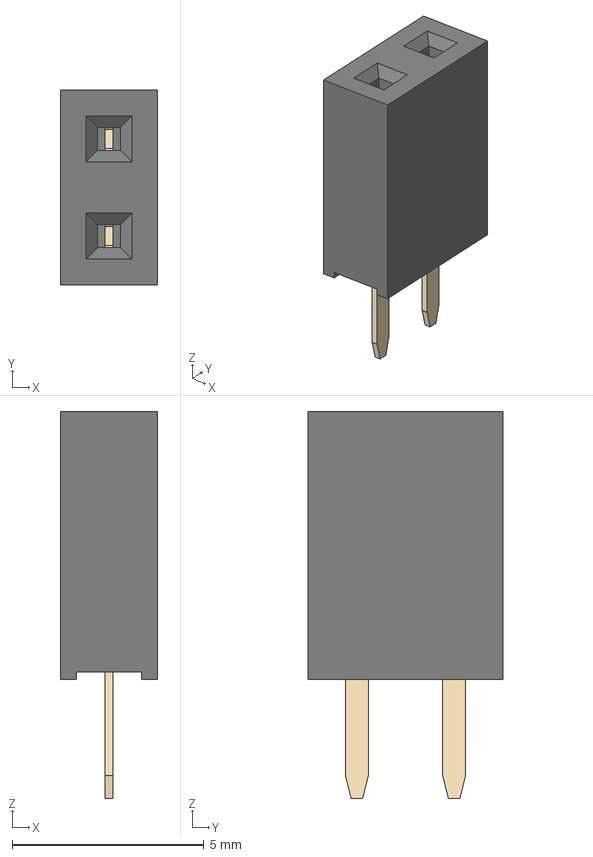
[picture p119: CAD file, 2022-07-30]
eda/hom3c0ming_boutonniere/3d_models/PinSocket_1x02_P2.54mm_Vertical.step
2.54 x 5.08 x 10.1 mm
