gowenrw/hom3c0ming_badge/eda/hom3c0ming_boutonniere/3d_models/Battery_Holder_3xAAA_Simple.step

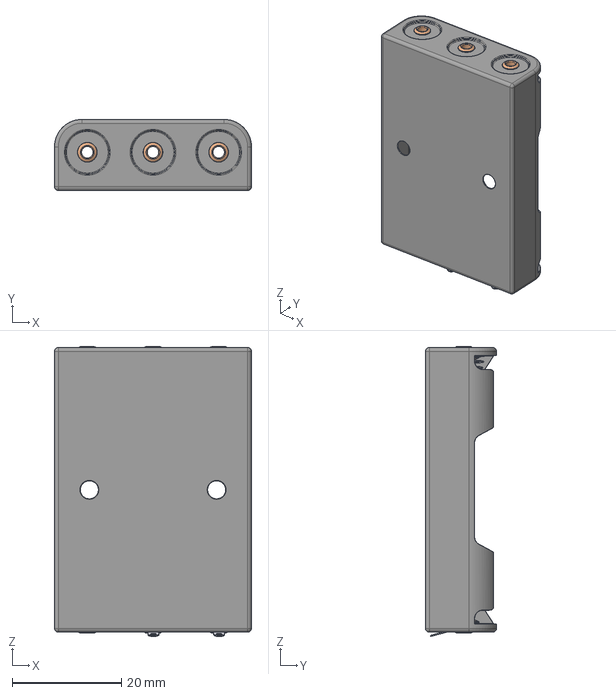
[picture p121: CAD file, 2022-07-30]
eda/hom3c0ming_boutonniere/3d_models/Battery_Holder_3xAAA_Simple.step
36.0 x 13.0 x 53.0 mm
