gowenrw/hom3c0ming_badge/eda/hom3c0ming_boutonniere/3d_models/LED_D5.0mm.step

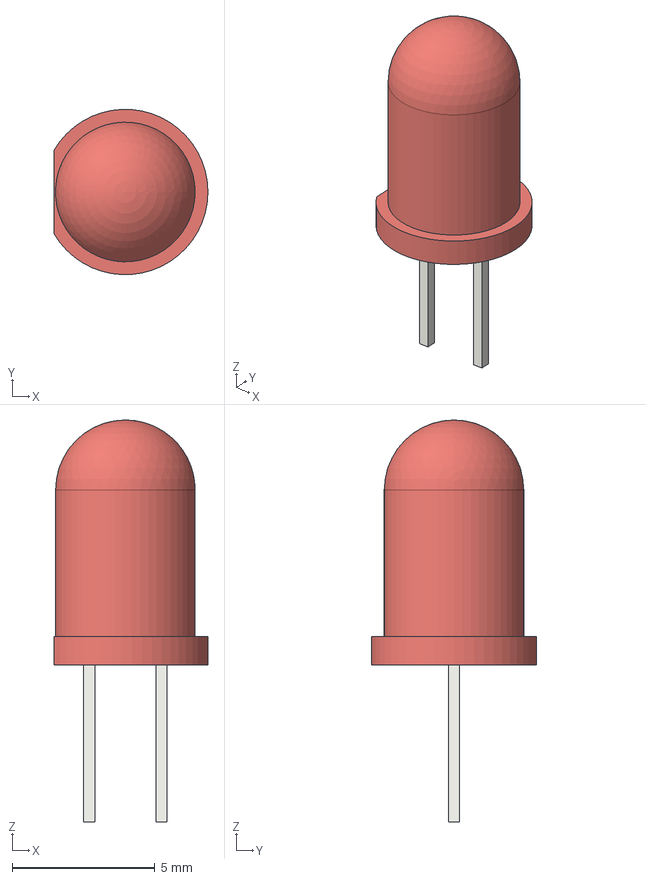
[picture p127: CAD file, 2022-07-30]
eda/hom3c0ming_boutonniere/3d_models/LED_D5.0mm.step
5.40 x 5.79 x 14.1 mm
