gowenrw/hom3c0ming_badge/eda/hom3c0ming_corsage/3d_models/BatteryHolder_2468_2xAAA.step

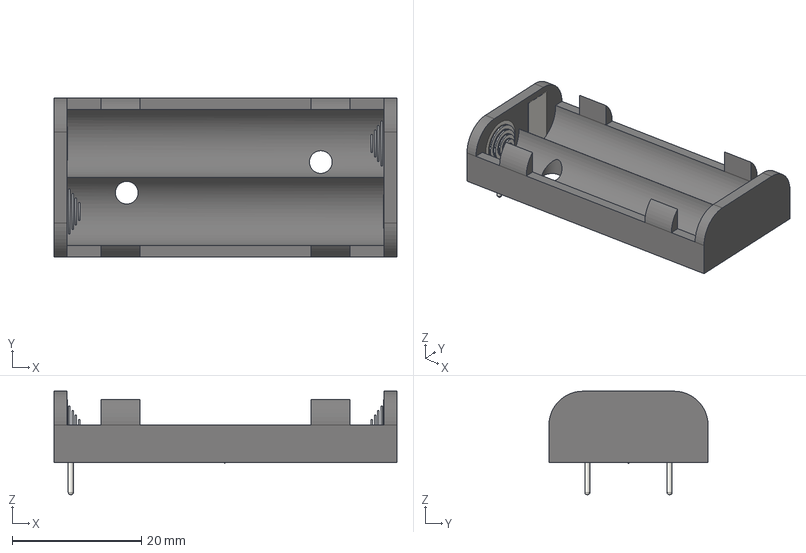
[picture p129: CAD file, 2022-07-30]
eda/hom3c0ming_corsage/3d_models/BatteryHolder_2468_2xAAA.step
53.0 x 24.6 x 16.0 mm
