gowenrw/hom3c0ming_badge/eda/hom3c0ming_boutonniere/3d_models/USB_Micro-B_Molex_47346-0001.step

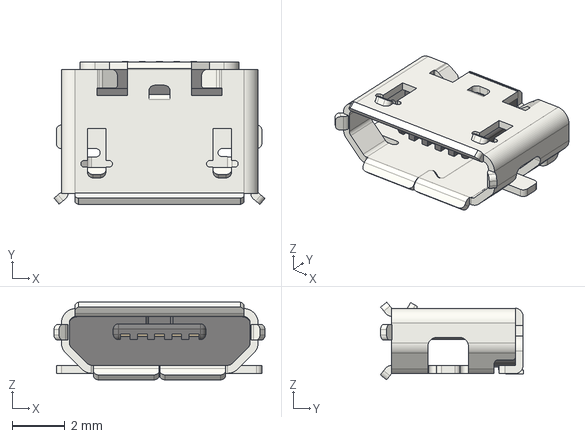
[picture p130: CAD file, 2022-07-30]
eda/hom3c0ming_boutonniere/3d_models/USB_Micro-B_Molex_47346-0001.step
7.98 x 5.42 x 2.94 mm
