gowenrw/hom3c0ming_badge/eda/hom3c0ming_boutonniere/3d_models/LED_D3.0mm.step

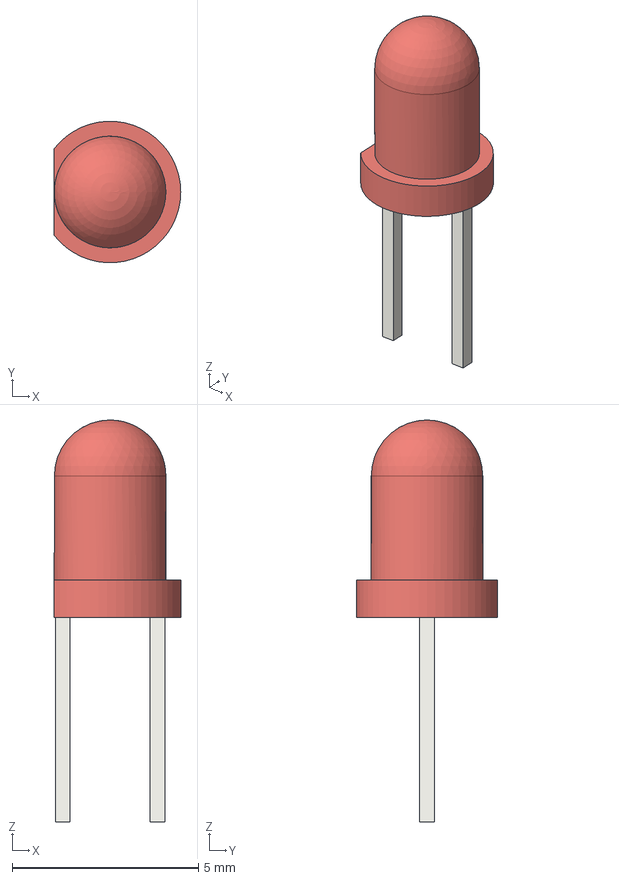
[picture p132: CAD file, 2022-07-30]
eda/hom3c0ming_boutonniere/3d_models/LED_D3.0mm.step
3.40 x 3.80 x 10.8 mm
