gowenrw/hom3c0ming_badge/eda/hom3c0ming_corsage/3d_models/SOIC-16_3.9x9.9mm_P1.27mm.step

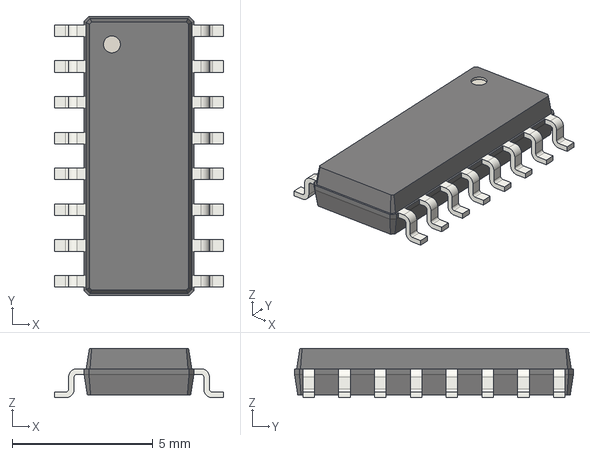
[picture p133: CAD file, 2022-07-30]
eda/hom3c0ming_corsage/3d_models/SOIC-16_3.9x9.9mm_P1.27mm.step
6.00 x 9.90 x 1.75 mm
