gowenrw/hom3c0ming_badge/eda/hom3c0ming_boutonniere/3d_models/TO-92_Inline.step

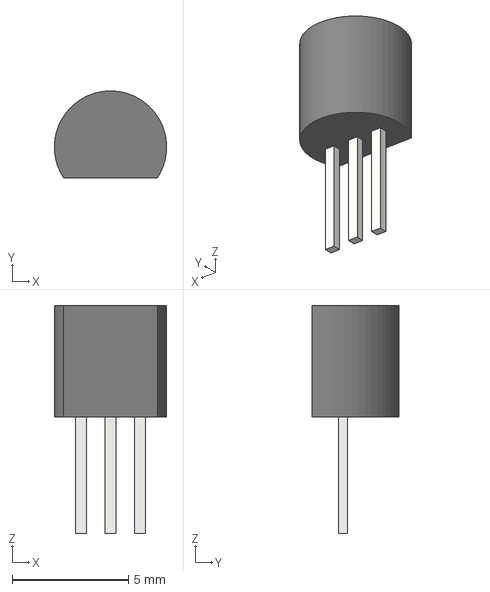
[picture p134: CAD file, 2022-07-30]
eda/hom3c0ming_boutonniere/3d_models/TO-92_Inline.step
4.83 x 3.74 x 9.80 mm
