gowenrw/hom3c0ming_badge/eda/hom3c0ming_boutonniere/hom3c0ming_boutonniere.sch

## KiCad design eda/hom3c0ming_boutonniere/hom3c0ming_boutonniere.sch (2022-07-30)

Schematic: hom3c0ming_boutonniere.sch

Parts:
BT1: Battery_CR2032; BatteryHolder_CR2032-BS-2-1_Front_backsilk
D1: LED_RGB_CC_5mm; LED_D5.0mm-4_RGB
D2: LED_3mm; LED_D3.0mm-2
J1: SAO_connector_v169bis; Badgelife-SAOv169-SAO-2x3-back-po
R1, R2, R3: 47; R_Axial_DIN0207_L6.3mm_D2.5mm_P7.62mm_Horizontal_backsilk
R4: 470; R_Axial_DIN0207_L6.3mm_D2.5mm_P7.62mm_Horizontal_backsilk
RV1, RV2, RV3: 0-10K; R_Potentiometer_3pin_THT_5mm_backsilk_anno
SW1: SW_SPDT_SS12D00G; SW_SPDT_Slide_SS12D00G-1P2T_3pin_back
