gowenrw/hom3c0ming_badge/eda/hom3c0ming_corsage/hom3c0ming_corsage.sch

## KiCad design eda/hom3c0ming_corsage/hom3c0ming_corsage.sch (2022-07-30)

Schematic: hom3c0ming_corsage.sch

Parts:
BT1: 2xAAA_3V; BatteryHolder_2468_2xAAA__1hole_back
BT2: 1xAAA_1.5V; BatteryHolder_2466_1xAAA_back
C501, C502, C601, C602: 100n; C_Disc_D3.0mm_W2.0mm_P2.50mm_backsilk
D1, D2, D3, D4: LED_Two_Color_CC_3mm; LED_D3.0mm-3-TwoColor_backsilk
D501, D502, D601, D602: WS2812D_RPIN_5mm; LED_D5.0mm-4_WS2812D_RPIN_backsilk
IC1: RPi_Pico_Back; RPi_Pico_THT_Back_headers
Q1: MOSFET_SOT23; Q_CJ3415_SOT-23-handsolder-back
R1: 22K; R_Axial_DIN0207_L6.3mm_D2.5mm_P7.62mm_Horizontal_backsilk
R2, R4, R6, R8, R10, R12, R14, R16, R181, R182, R201, R202: 470; R_Axial_DIN0207_L6.3mm_D2.5mm_P7.62mm_Horizontal_backsilk
SW1: SW_SPDT_SS12D00G; SW_SPDT_Slide_SS12D00G-1P2T_3pin_back

Notes on the sheet:
D4b pwm0a
D1a pwm1a
D1b pwm2a
D2a pwm3a
D2b pwm4a
D3a pwm5a
D3b pwm6a
D4a pwm7a
D5xx strip
D6xx strip
GREEN
POWER PROTECTION
BLUE
