gowenrw/hom3c0ming_badge/docs/images/20220730_112637.jpg

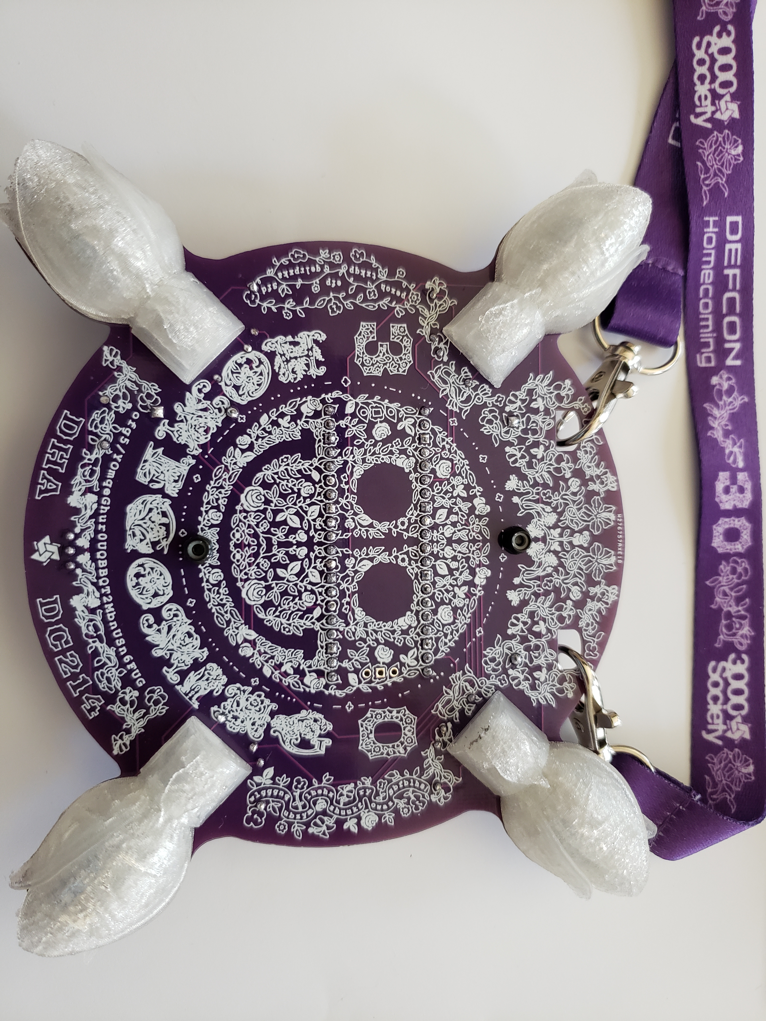
docs/images/20220730_112637.jpg
