gowenrw/hom3c0ming_badge/docs/images/20220730_112945.jpg

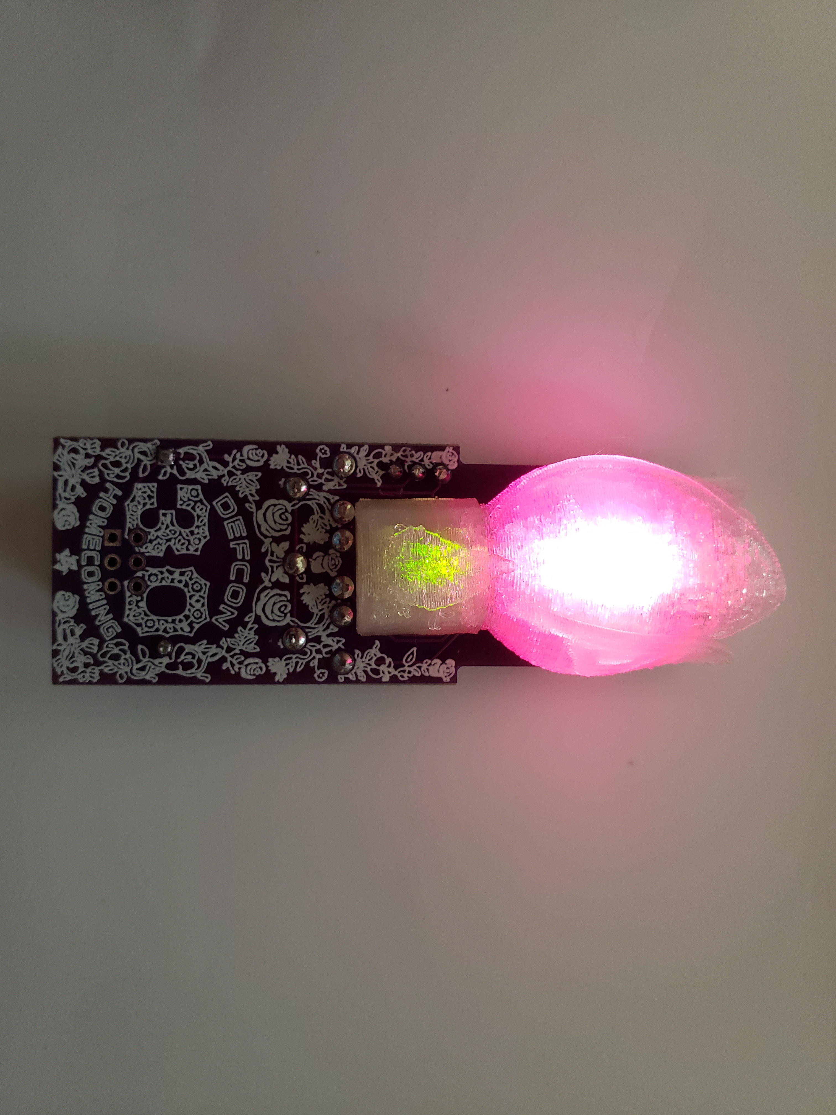
docs/images/20220730_112945.jpg
