gowenrw/hom3c0ming_badge/docs/images/20220730_114001.jpg

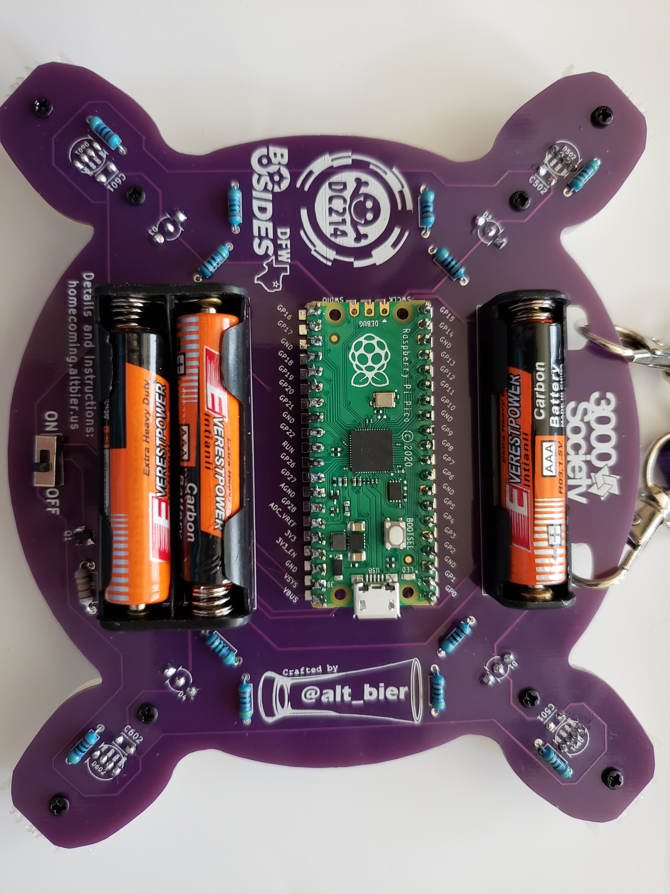
docs/images/20220730_114001.jpg
